TheSuperPixel/Embedded_Core_Boards/STM32H750/测试例程/DCMI-摄像头OV5640驱动/图像显示到800x480分辨率的屏幕/移植注意事项3.png

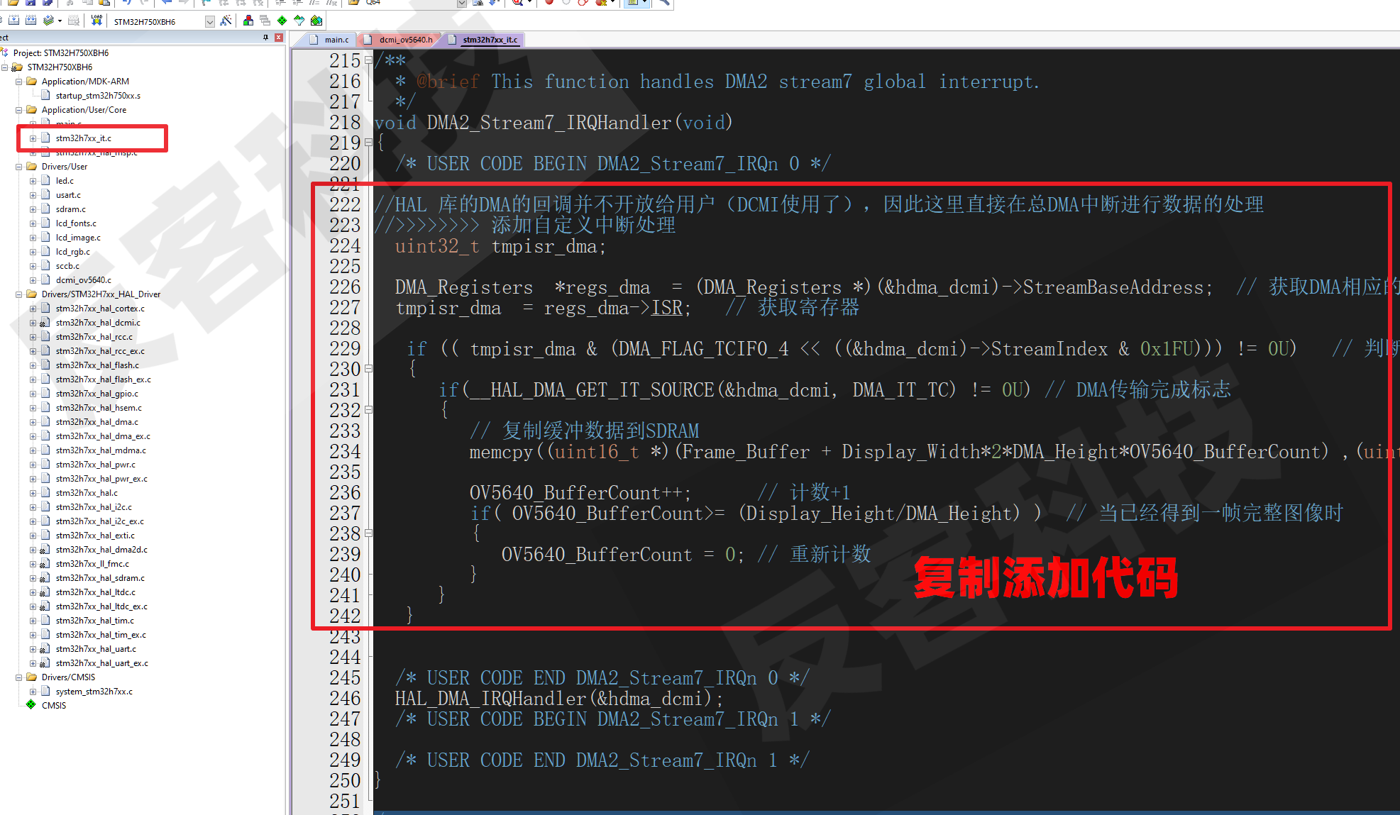
STM32H750/测试例程/DCMI-摄像头OV5640驱动/图像显示到800x480分辨率的屏幕/移植注意事项3.png
