TheSuperPixel/Embedded_Core_Boards/STM32H750/外壳/底板.SLDPRT

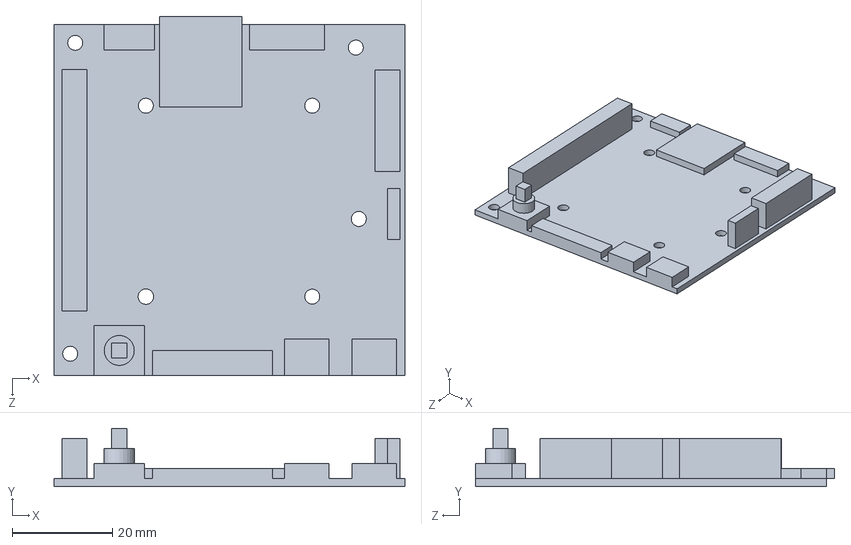
[picture p26: CAD file, 2026-02-05]
STM32H750/外壳/底板.SLDPRT
70.0 x 11.6 x 71.6 mm
