TheSuperPixel/Embedded_Core_Boards/XC7A35T/外壳/PCIE版本/输出图纸/中层亚克力.DXF

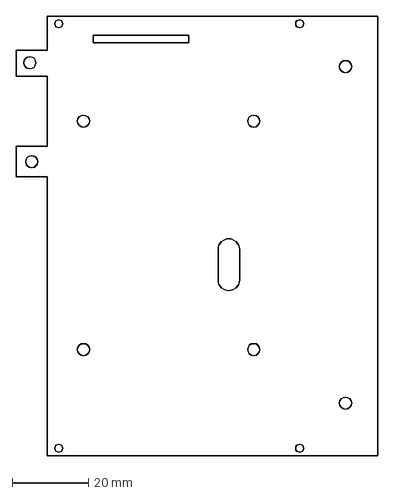
[picture p29: CAD file, 2026-03-31]
XC7A35T/外壳/PCIE版本/输出图纸/中层亚克力.DXF
94.6 x 115.0 mm
