TheSuperPixel/Embedded_Core_Boards/XC7A35T/外壳/全排针版本/底部亚克力.SLDPRT

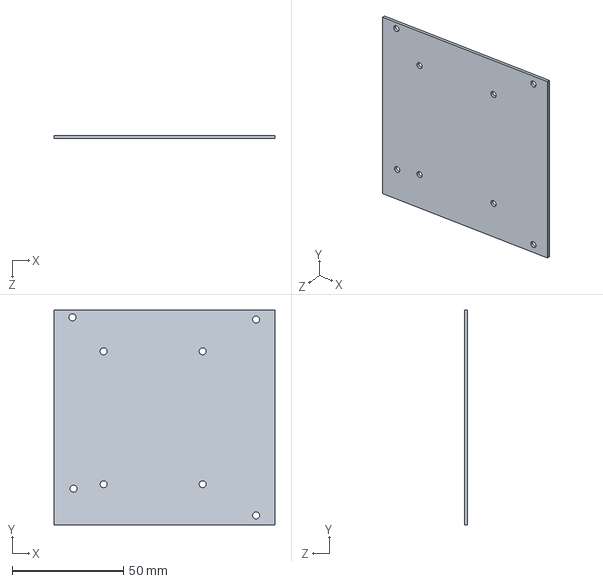
[picture p30: CAD file, 2026-02-06]
XC7A35T/外壳/全排针版本/底部亚克力.SLDPRT
99.3 x 96.6 x 1.50 mm
