TheSuperPixel/Embedded_Core_Boards/RK3588/外壳/输出图纸/MIPI屏幕亚克力.DXF

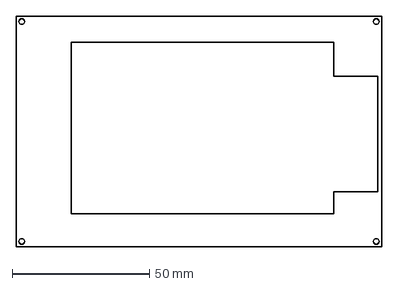
[picture p32: CAD file, 2026-03-31]
RK3588/外壳/输出图纸/MIPI屏幕亚克力.DXF
133.0 x 84.0 mm
