TheSuperPixel/Embedded_Core_Boards/STM32H750/外壳/输出图纸/顶层亚克力.DXF

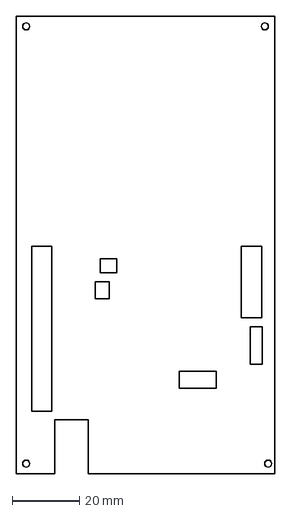
[picture p33: CAD file, 2026-03-31]
STM32H750/外壳/输出图纸/顶层亚克力.DXF
77.0 x 136.0 mm
