TheSuperPixel/Embedded_Core_Boards/XC7A35T/外壳/全排针版本/底部铜柱.SLDPRT

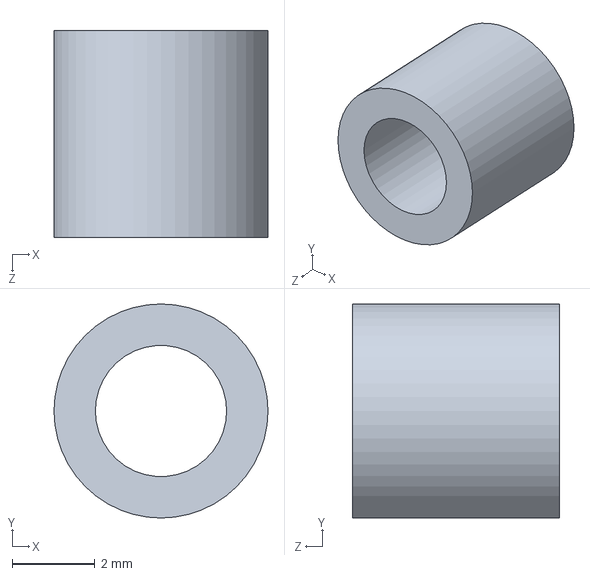
[picture p35: CAD file, 2026-02-06]
XC7A35T/外壳/全排针版本/底部铜柱.SLDPRT
5.17 x 5.17 x 5.00 mm
