TheSuperPixel/Embedded_Core_Boards/RK3588/外壳/输出图纸/底层亚克力.DXF

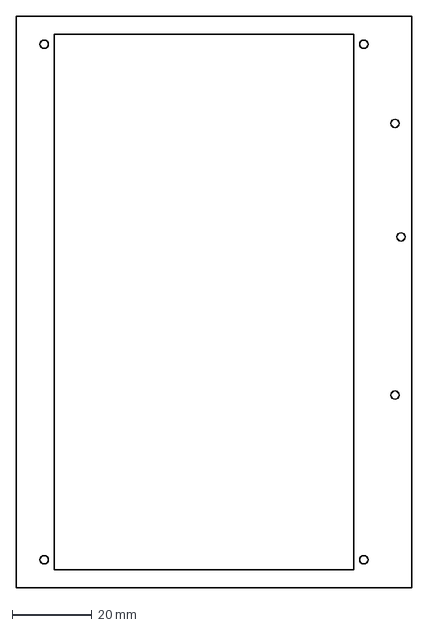
[picture p36: CAD file, 2026-03-31]
RK3588/外壳/输出图纸/底层亚克力.DXF
99.0 x 143.0 mm
