TheSuperPixel/Embedded_Core_Boards/XC7A35T/外壳/PCIE版本/输出图纸/顶层亚克力_无散热.DXF

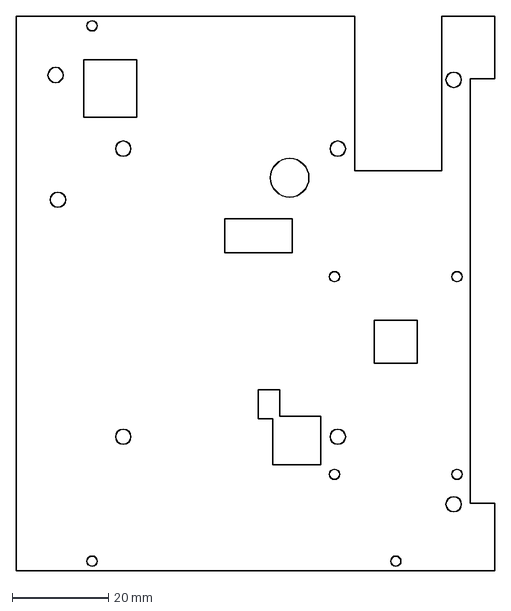
[picture p38: CAD file, 2026-03-31]
XC7A35T/外壳/PCIE版本/输出图纸/顶层亚克力_无散热.DXF
99.2 x 115.0 mm
