TheSuperPixel/Embedded_Core_Boards/XC7A35T/外壳/全排针版本/底板.SLDPRT

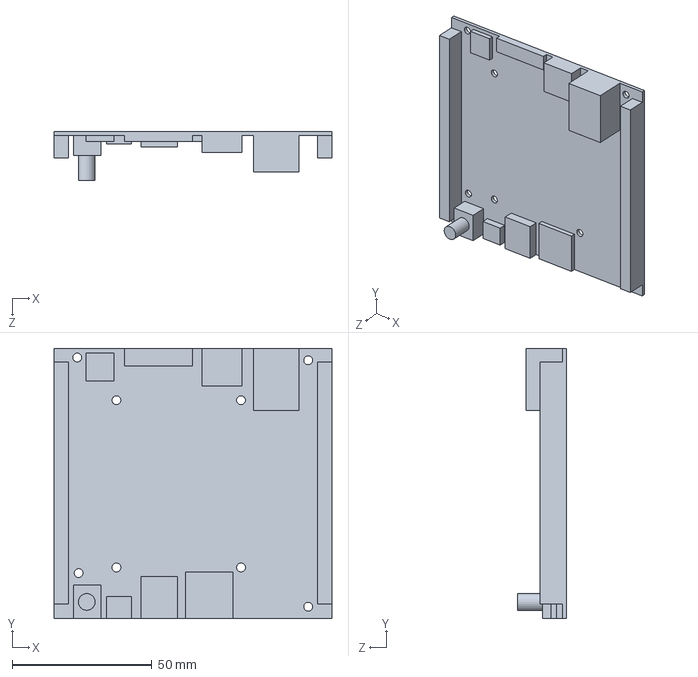
[picture p40: CAD file, 2026-02-06]
XC7A35T/外壳/全排针版本/底板.SLDPRT
99.3 x 96.6 x 17.5 mm
