TheSuperPixel/Embedded_Core_Boards/RK3588/外壳/MIPI屏幕.SLDPRT

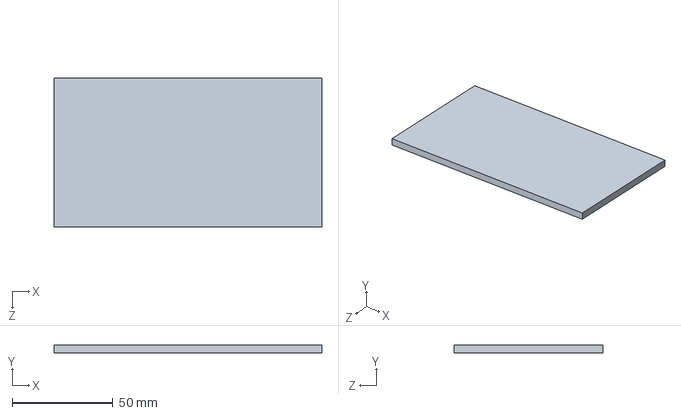
[picture p41: CAD file, 2026-02-09]
RK3588/外壳/MIPI屏幕.SLDPRT
133.0 x 4.00 x 74.0 mm
