TheSuperPixel/Embedded_Core_Boards/STM32H750/外壳/4.3寸RGB驱动.SLDPRT

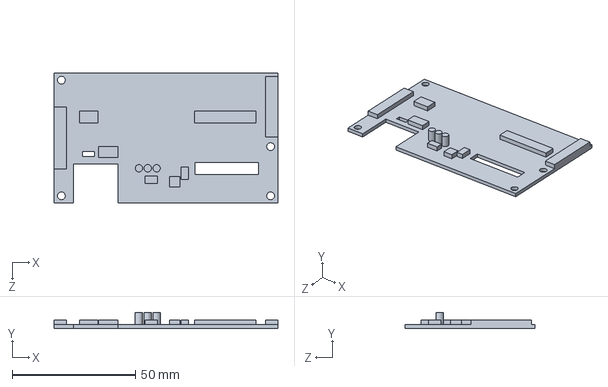
[picture p44: CAD file, 2026-02-05]
STM32H750/外壳/4.3寸RGB驱动.SLDPRT
91.0 x 6.60 x 53.0 mm
