TheSuperPixel/Embedded_Core_Boards/XC7A35T/外壳/PCIE版本/底层亚克力.SLDPRT

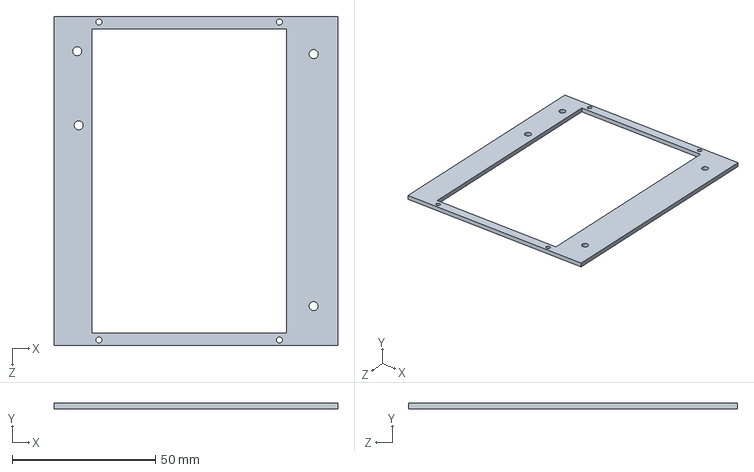
[picture p45: CAD file, 2026-02-06]
XC7A35T/外壳/PCIE版本/底层亚克力.SLDPRT
99.2 x 2.00 x 115.0 mm
