TheSuperPixel/Embedded_Core_Boards/STM32H750/外壳/OLED屏幕.SLDPRT

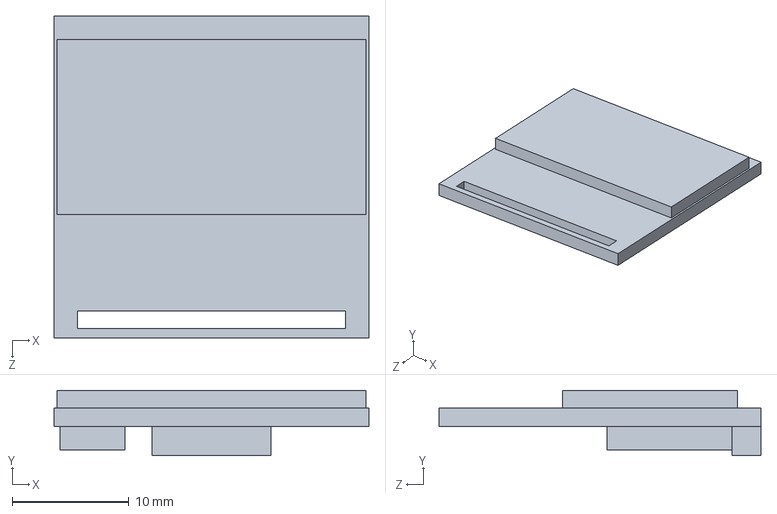
[picture p47: CAD file, 2026-02-05]
STM32H750/外壳/OLED屏幕.SLDPRT
27.0 x 5.60 x 27.6 mm
