TheSuperPixel/Embedded_Core_Boards/XC7A35T/外壳/全排针版本/顶部铜柱.SLDPRT

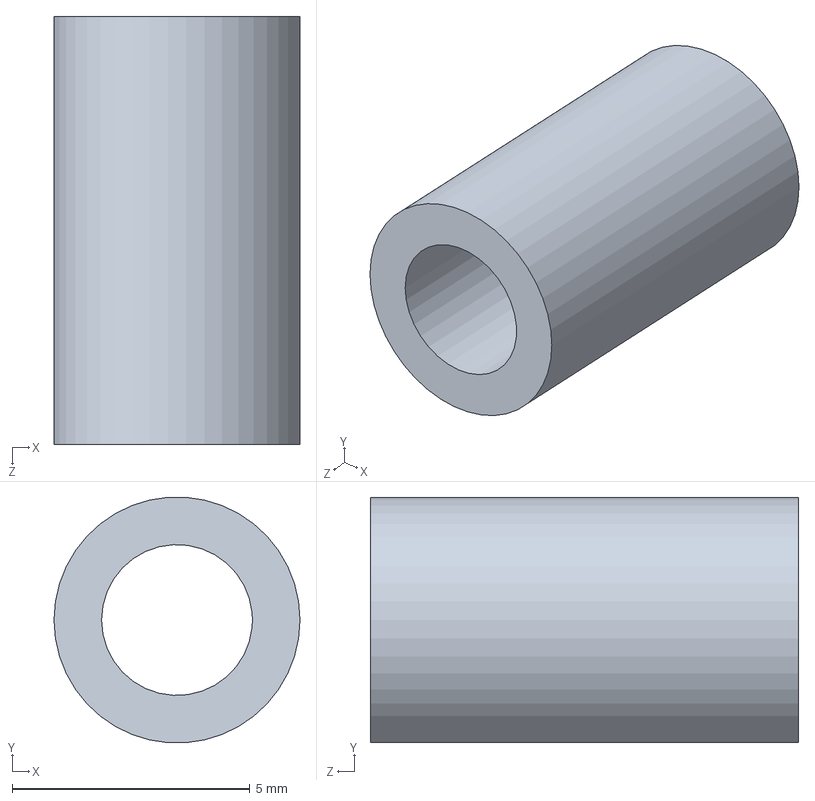
[picture p48: CAD file, 2026-02-06]
XC7A35T/外壳/全排针版本/顶部铜柱.SLDPRT
5.17 x 5.16 x 9.00 mm
