TheSuperPixel/Embedded_Core_Boards/RK3588/外壳/底板.SLDPRT

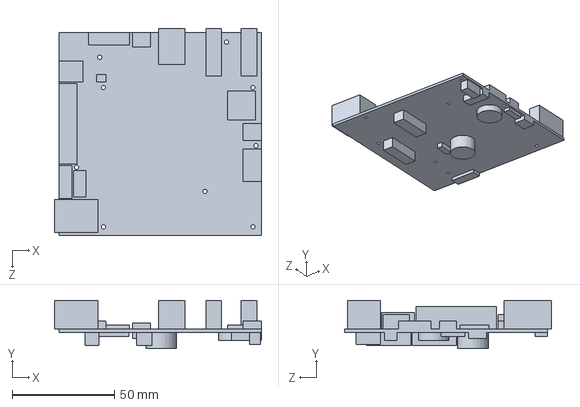
[picture p49: CAD file, 2026-02-09]
RK3588/外壳/底板.SLDPRT
101.1 x 23.6 x 101.0 mm
