TheSuperPixel/Embedded_Core_Boards/RK3588/外壳/风扇.SLDPRT

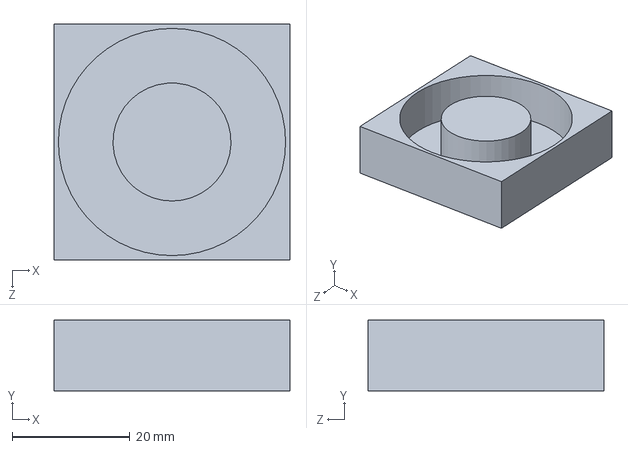
[picture p50: CAD file, 2026-02-09]
RK3588/外壳/风扇.SLDPRT
40.0 x 12.0 x 40.0 mm
