TheSuperPixel/Embedded_Core_Boards/STM32H750/外壳/核心板.SLDPRT

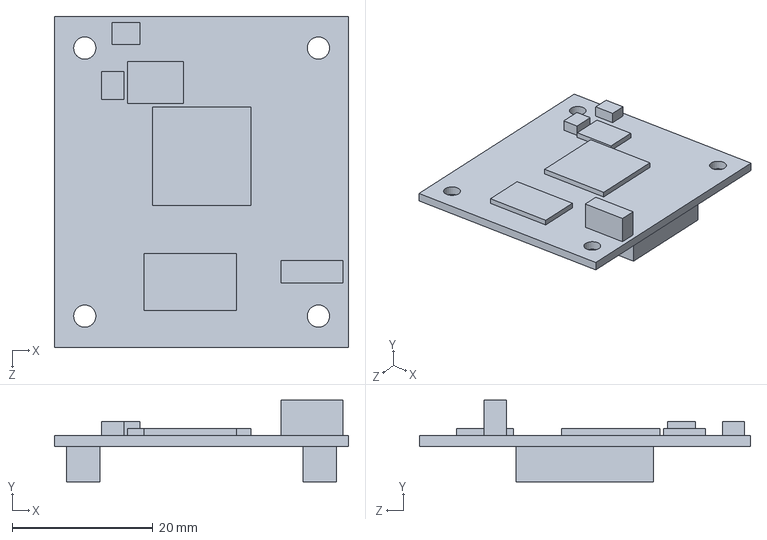
[picture p52: CAD file, 2026-02-05]
STM32H750/外壳/核心板.SLDPRT
41.9 x 11.6 x 47.1 mm
