TheSuperPixel/Embedded_Core_Boards/RK3588/外壳/镜头模组.SLDPRT

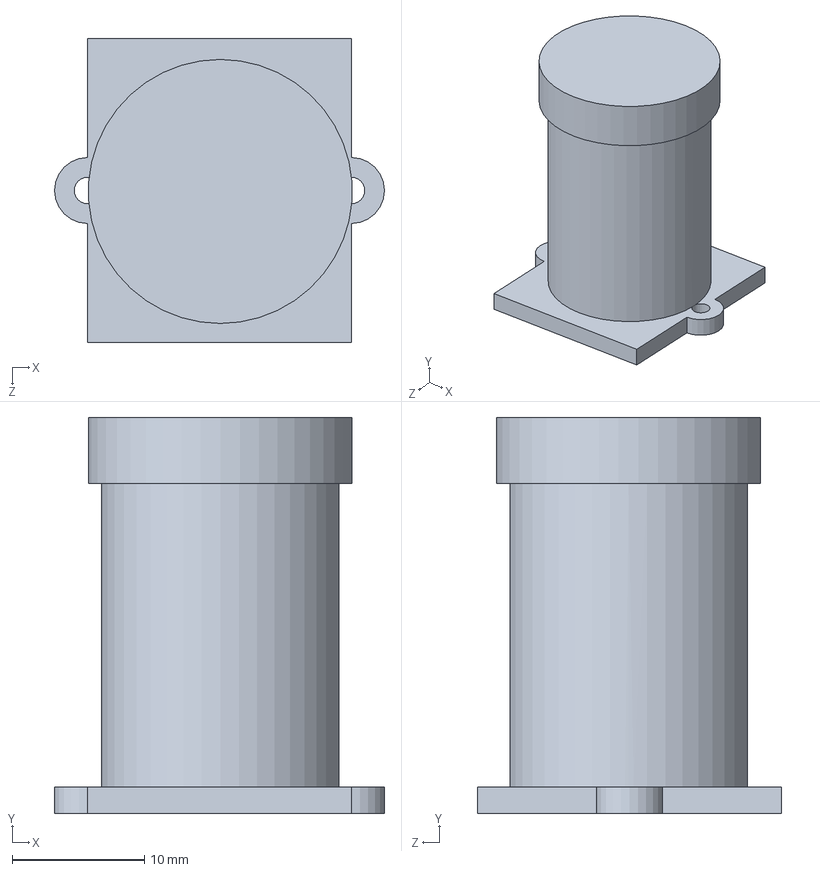
[picture p53: CAD file, 2026-02-09]
RK3588/外壳/镜头模组.SLDPRT
25.0 x 30.0 x 23.0 mm
