TheSuperPixel/Embedded_Core_Boards/STM32H750/外壳/MCU LCD屏幕.SLDPRT

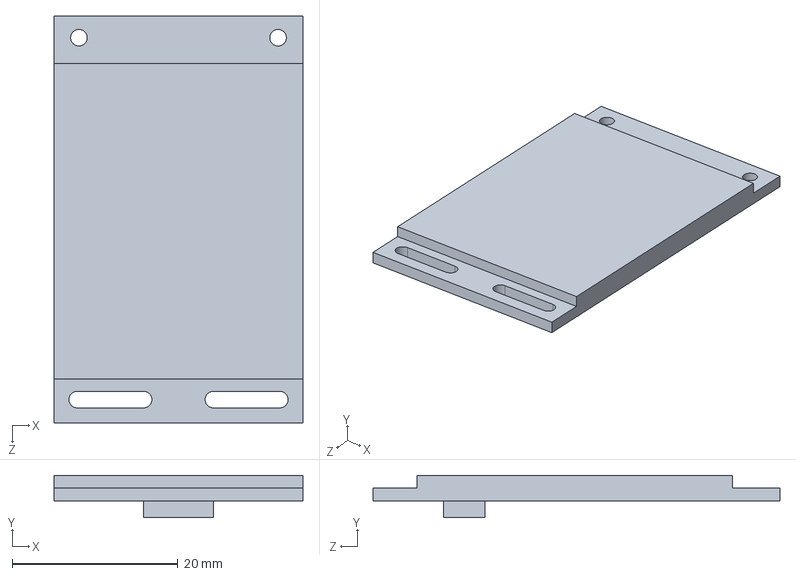
[picture p54: CAD file, 2026-02-05]
STM32H750/外壳/MCU LCD屏幕.SLDPRT
30.0 x 5.10 x 49.0 mm
