TheSuperPixel/Embedded_Core_Boards/XC7A35T/外壳/PCIE版本/底板_PCIE.SLDPRT

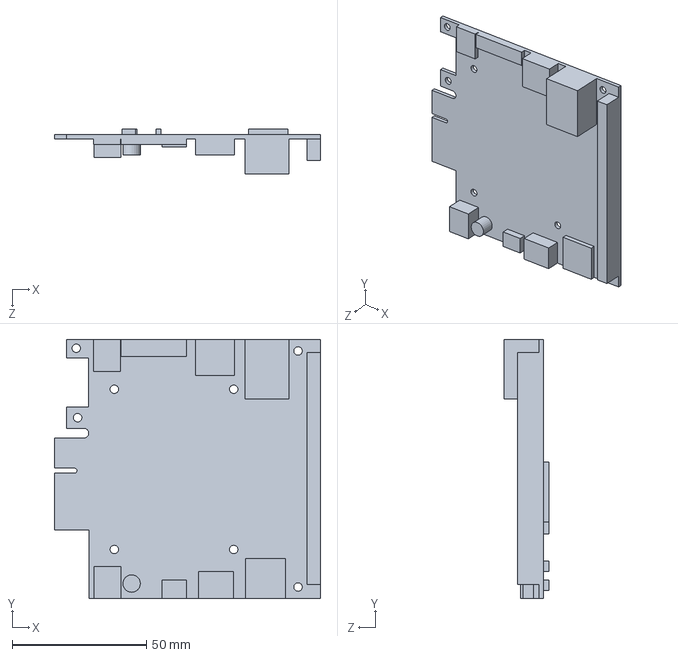
[picture p55: CAD file, 2026-02-06]
XC7A35T/外壳/PCIE版本/底板_PCIE.SLDPRT
99.2 x 96.6 x 16.6 mm
