TheSuperPixel/Embedded_Core_Boards/RK3588/外壳/顶层亚克力.SLDPRT

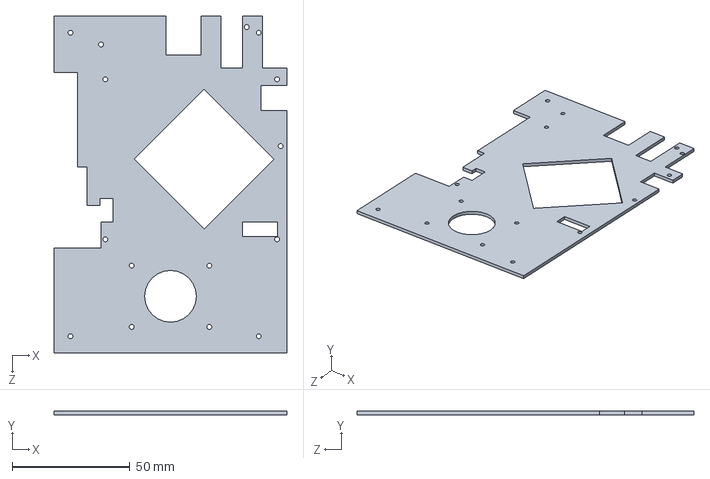
[picture p56: CAD file, 2026-02-09]
RK3588/外壳/顶层亚克力.SLDPRT
99.0 x 1.60 x 143.0 mm
