TheSuperPixel/Embedded_Core_Boards/STM32H750/外壳/OV5640摄像头.SLDPRT

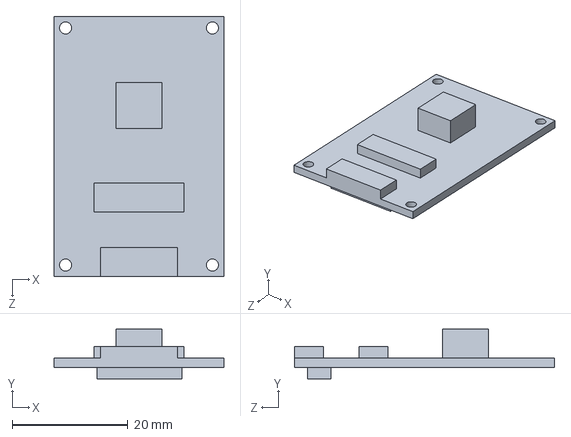
[picture p57: CAD file, 2026-02-05]
STM32H750/外壳/OV5640摄像头.SLDPRT
29.4 x 8.60 x 45.0 mm
