TheSuperPixel/Embedded_Core_Boards/RK3588/外壳/核心板.SLDPRT

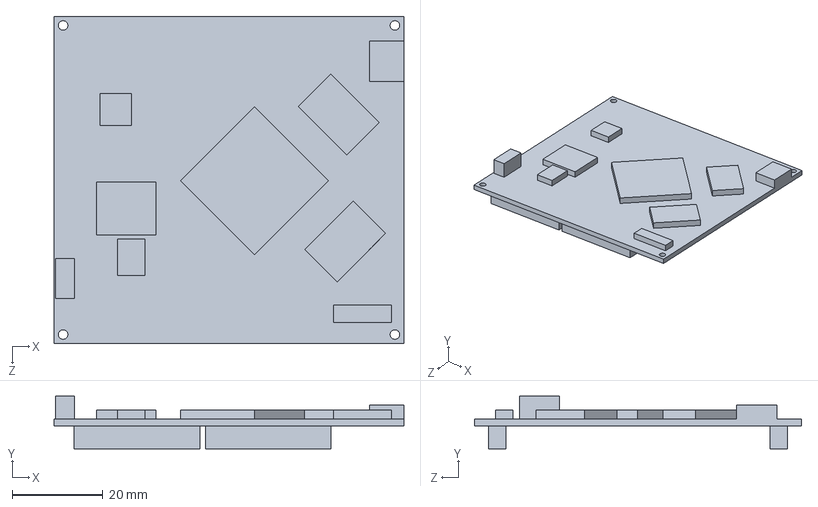
[picture p58: CAD file, 2026-02-09]
RK3588/外壳/核心板.SLDPRT
77.0 x 11.6 x 72.0 mm
