TheSuperPixel/Embedded_Core_Boards/STM32H750/外壳/中层亚克力.SLDPRT

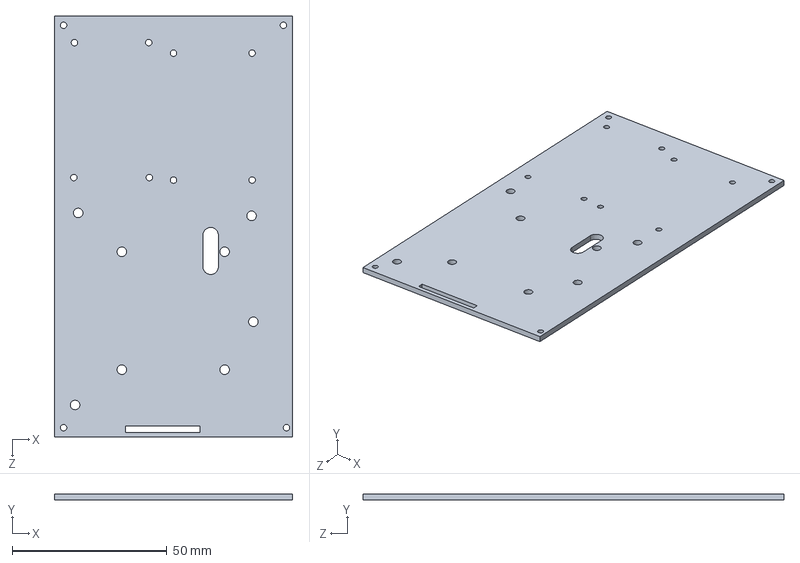
[picture p59: CAD file, 2026-02-05]
STM32H750/外壳/中层亚克力.SLDPRT
77.0 x 2.00 x 136.0 mm
