TheSuperPixel/Embedded_Core_Boards/XC7A35T/外壳/PCIE版本/核心板.SLDPRT

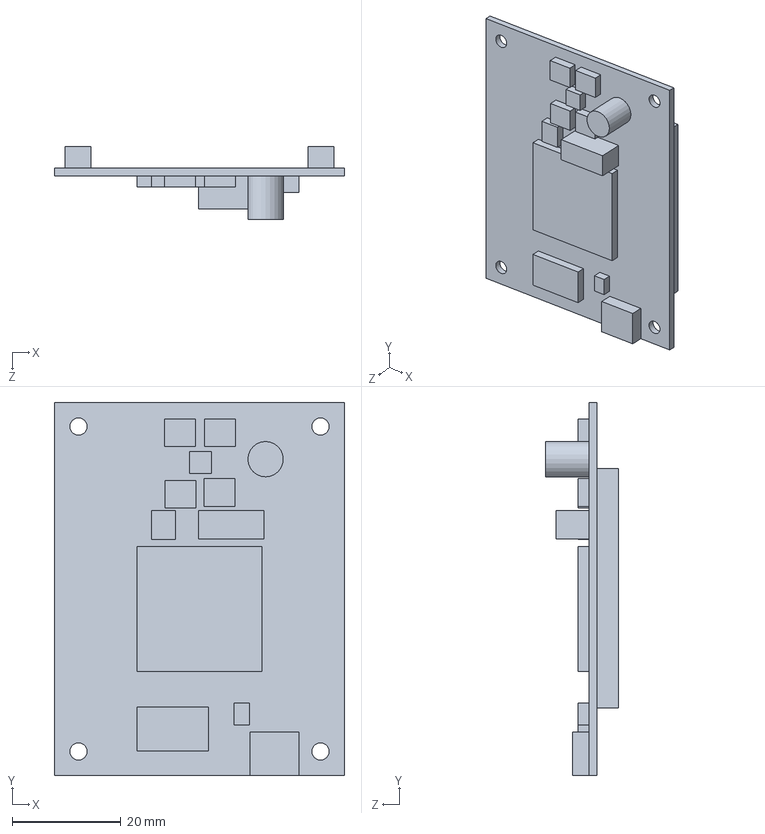
[picture p60: CAD file, 2026-02-06]
XC7A35T/外壳/PCIE版本/核心板.SLDPRT
53.3 x 68.6 x 13.5 mm
