TheSuperPixel/Embedded_Core_Boards/XC7A35T/外壳/PCIE版本/4.3寸RGB屏幕.SLDPRT

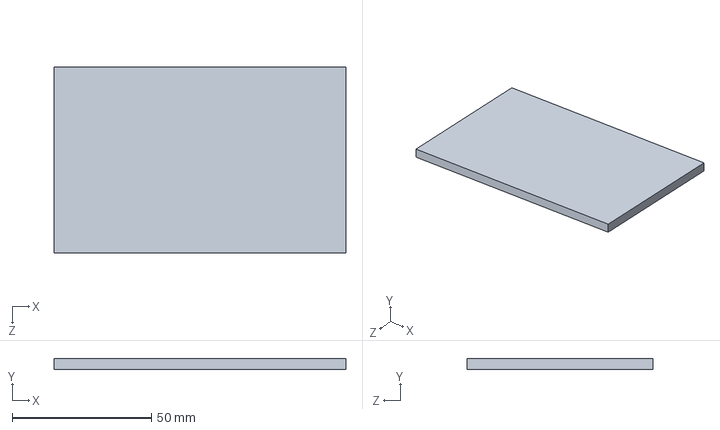
[picture p61: CAD file, 2026-02-05]
XC7A35T/外壳/PCIE版本/4.3寸RGB屏幕.SLDPRT
105.0 x 4.00 x 67.0 mm
