TheSuperPixel/Embedded_Core_Boards/XC7A35T/外壳/PCIE版本/屏幕亚克力.SLDPRT

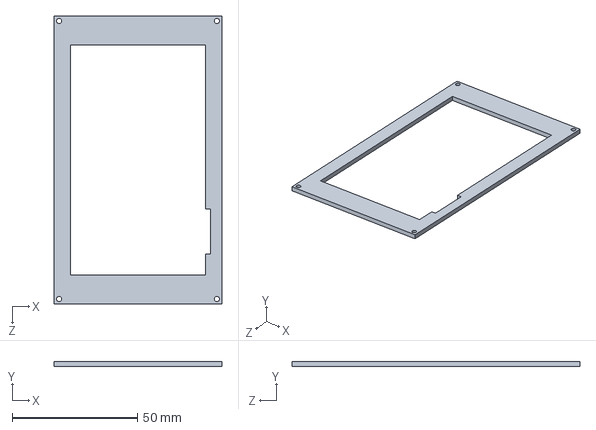
[picture p62: CAD file, 2026-02-05]
XC7A35T/外壳/PCIE版本/屏幕亚克力.SLDPRT
67.0 x 2.00 x 115.0 mm
