TheSuperPixel/Embedded_Core_Boards/RK3588/外壳/MIPI屏幕亚克力.SLDPRT

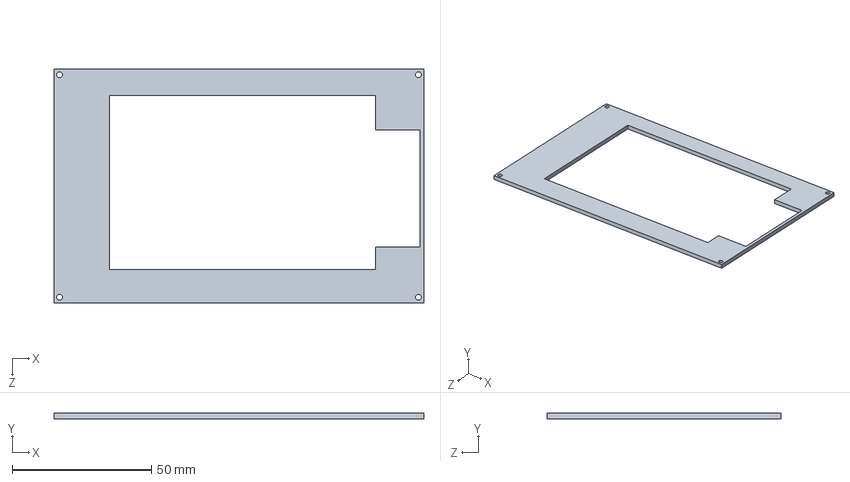
[picture p63: CAD file, 2026-02-09]
RK3588/外壳/MIPI屏幕亚克力.SLDPRT
133.0 x 2.00 x 84.0 mm
