TheSuperPixel/Embedded_Core_Boards/XC7A35T/XC7A35T核心板/Project Outputs for xc7a35t/Sheet1.pdf

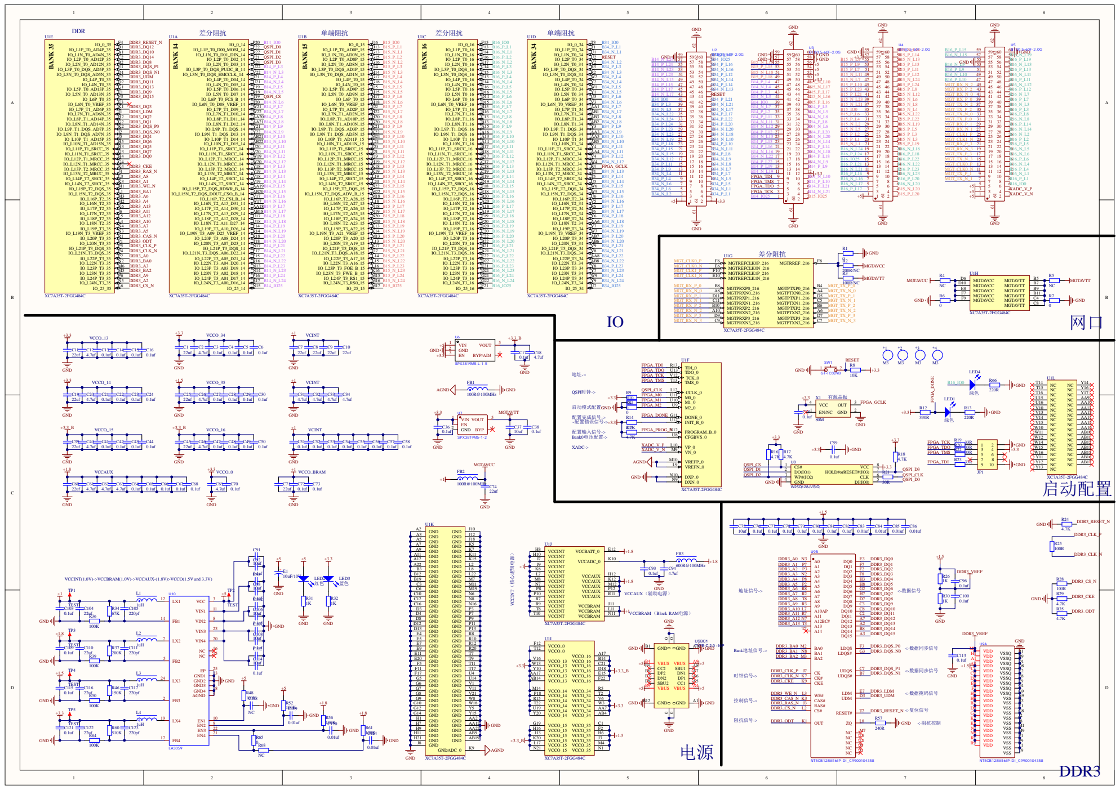
[picture p111: page 1]

VCCINT(1.0V)->VCCBRAM(1.0V)->VCCAUX-(1.8V)>VCCO(1.5V and 3.3V)
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
