TheSuperPixel/Embedded_Core_Boards/STM32H750/底板v2/Project Outputs for STM32H750底板/Sheet1.pdf

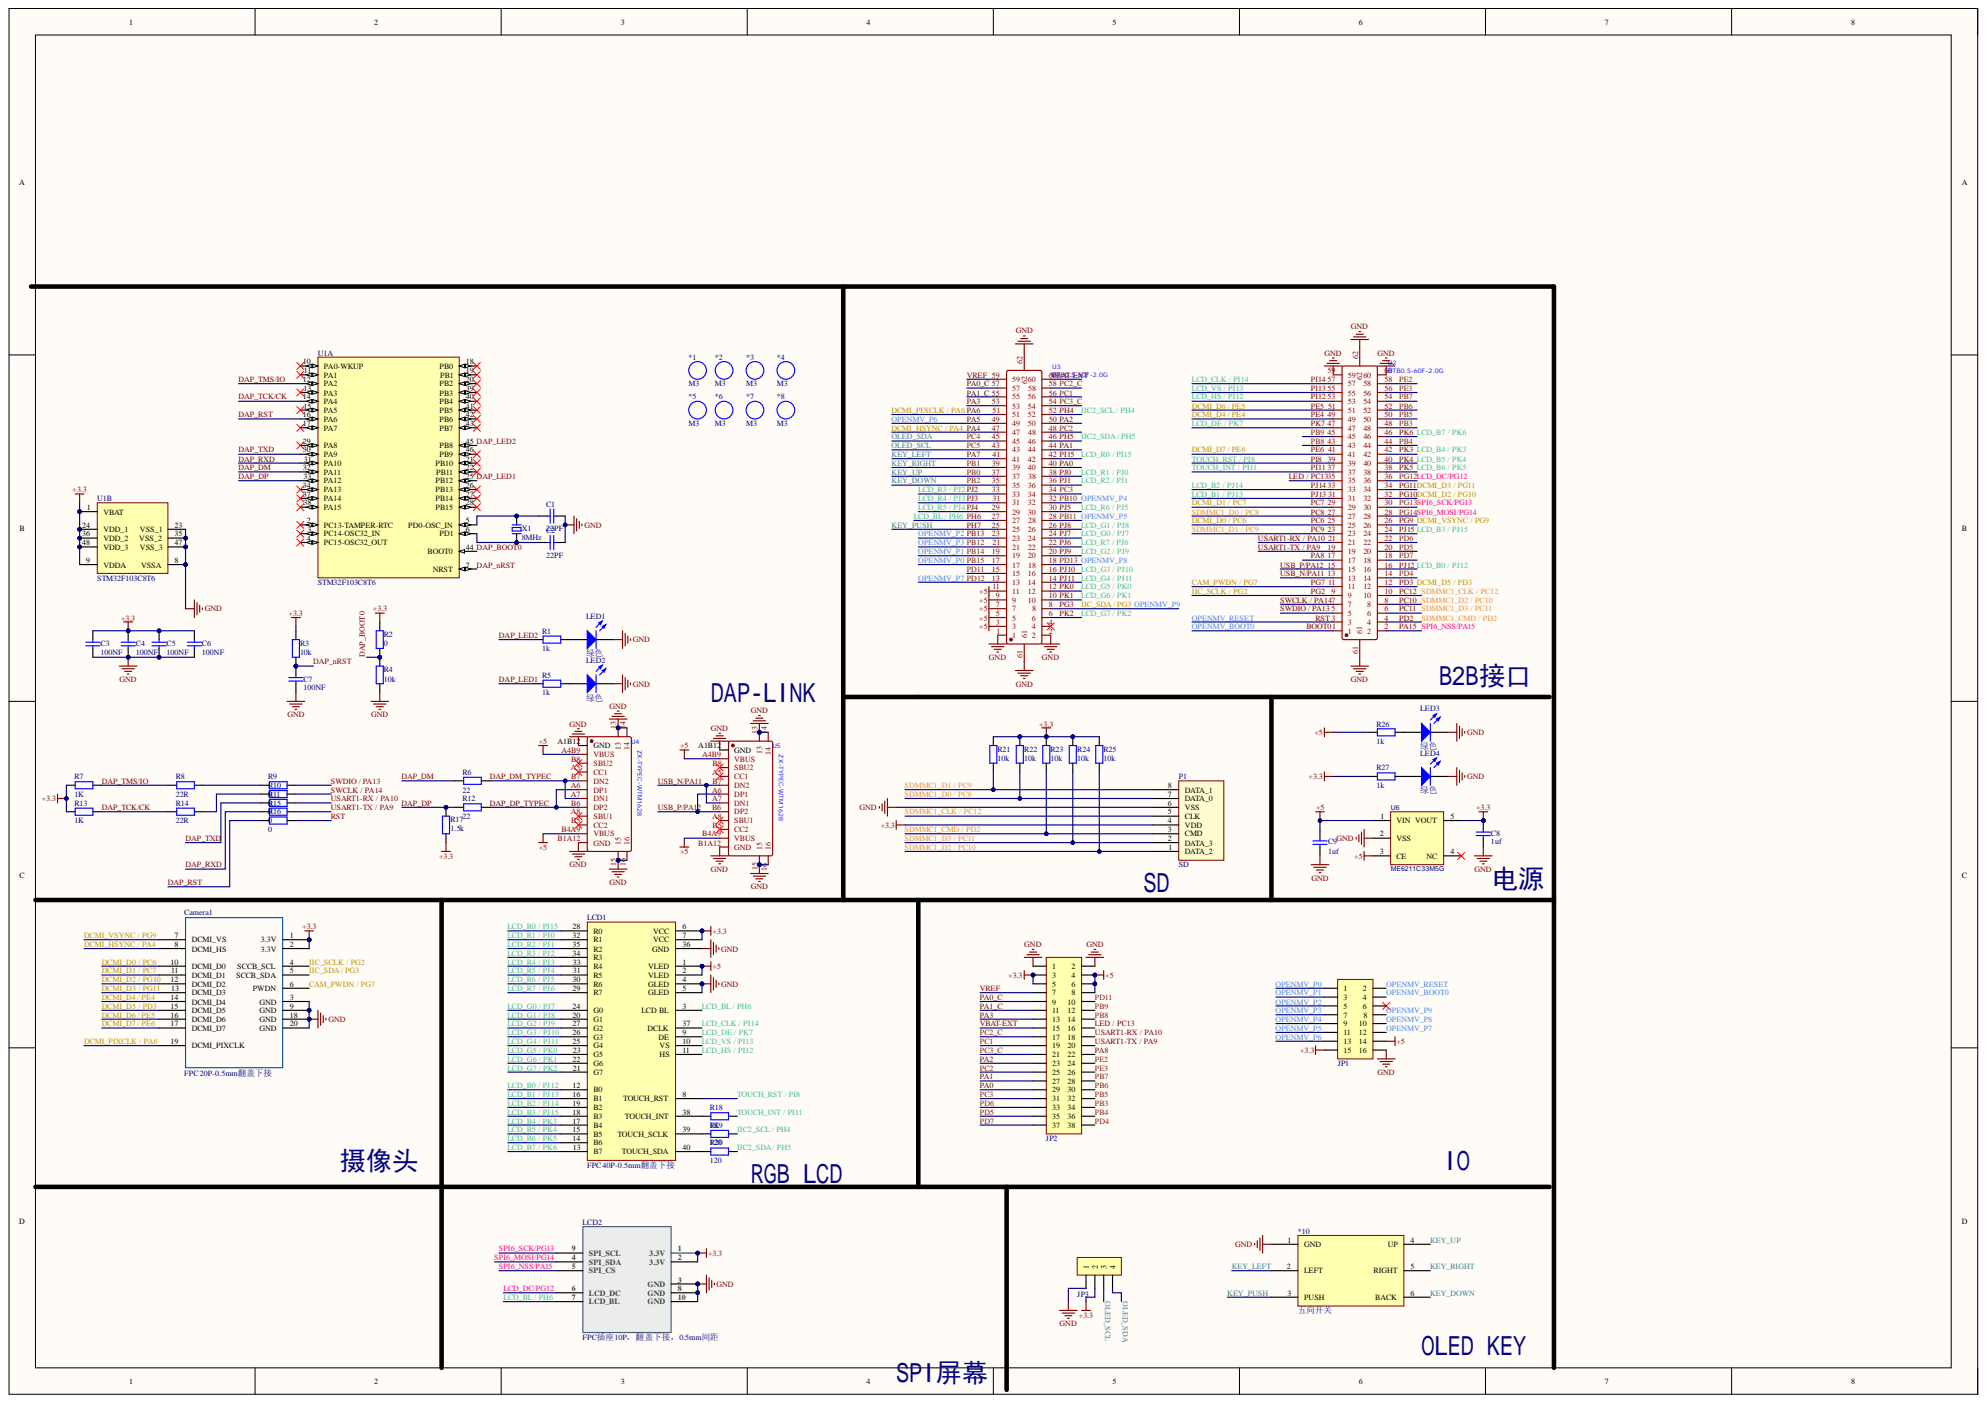
[picture p124: page 1]
