TheSuperPixel/Embedded_Core_Boards/XC7A35T/XC7A35T底板v1/Project Outputs for XC7A35T底板/Sheet1.pdf

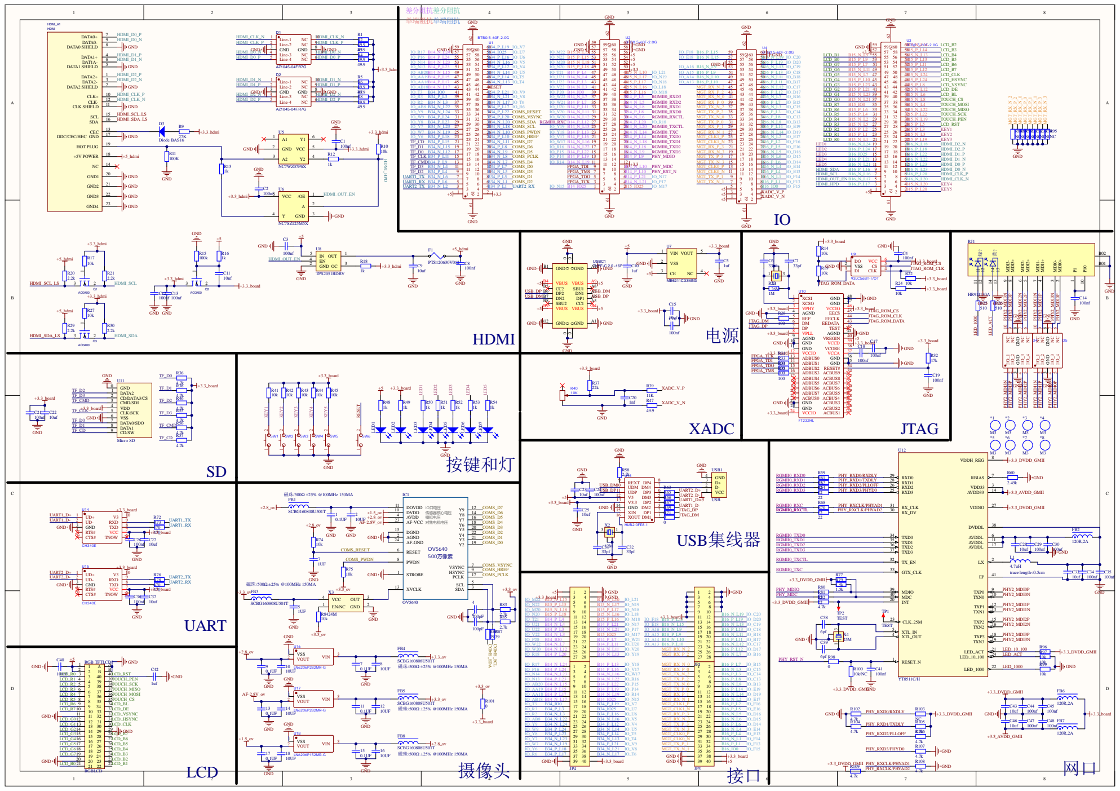
[picture p125: page 1]

I/O_4 5 NC 6 NC 7 GND 8 NC 9 NC 10
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
