TheSuperPixel/Embedded_Core_Boards/STM32H750/STM32H750核心板v1/Project Outputs for STM32H750核心板/Sheet1.pdf

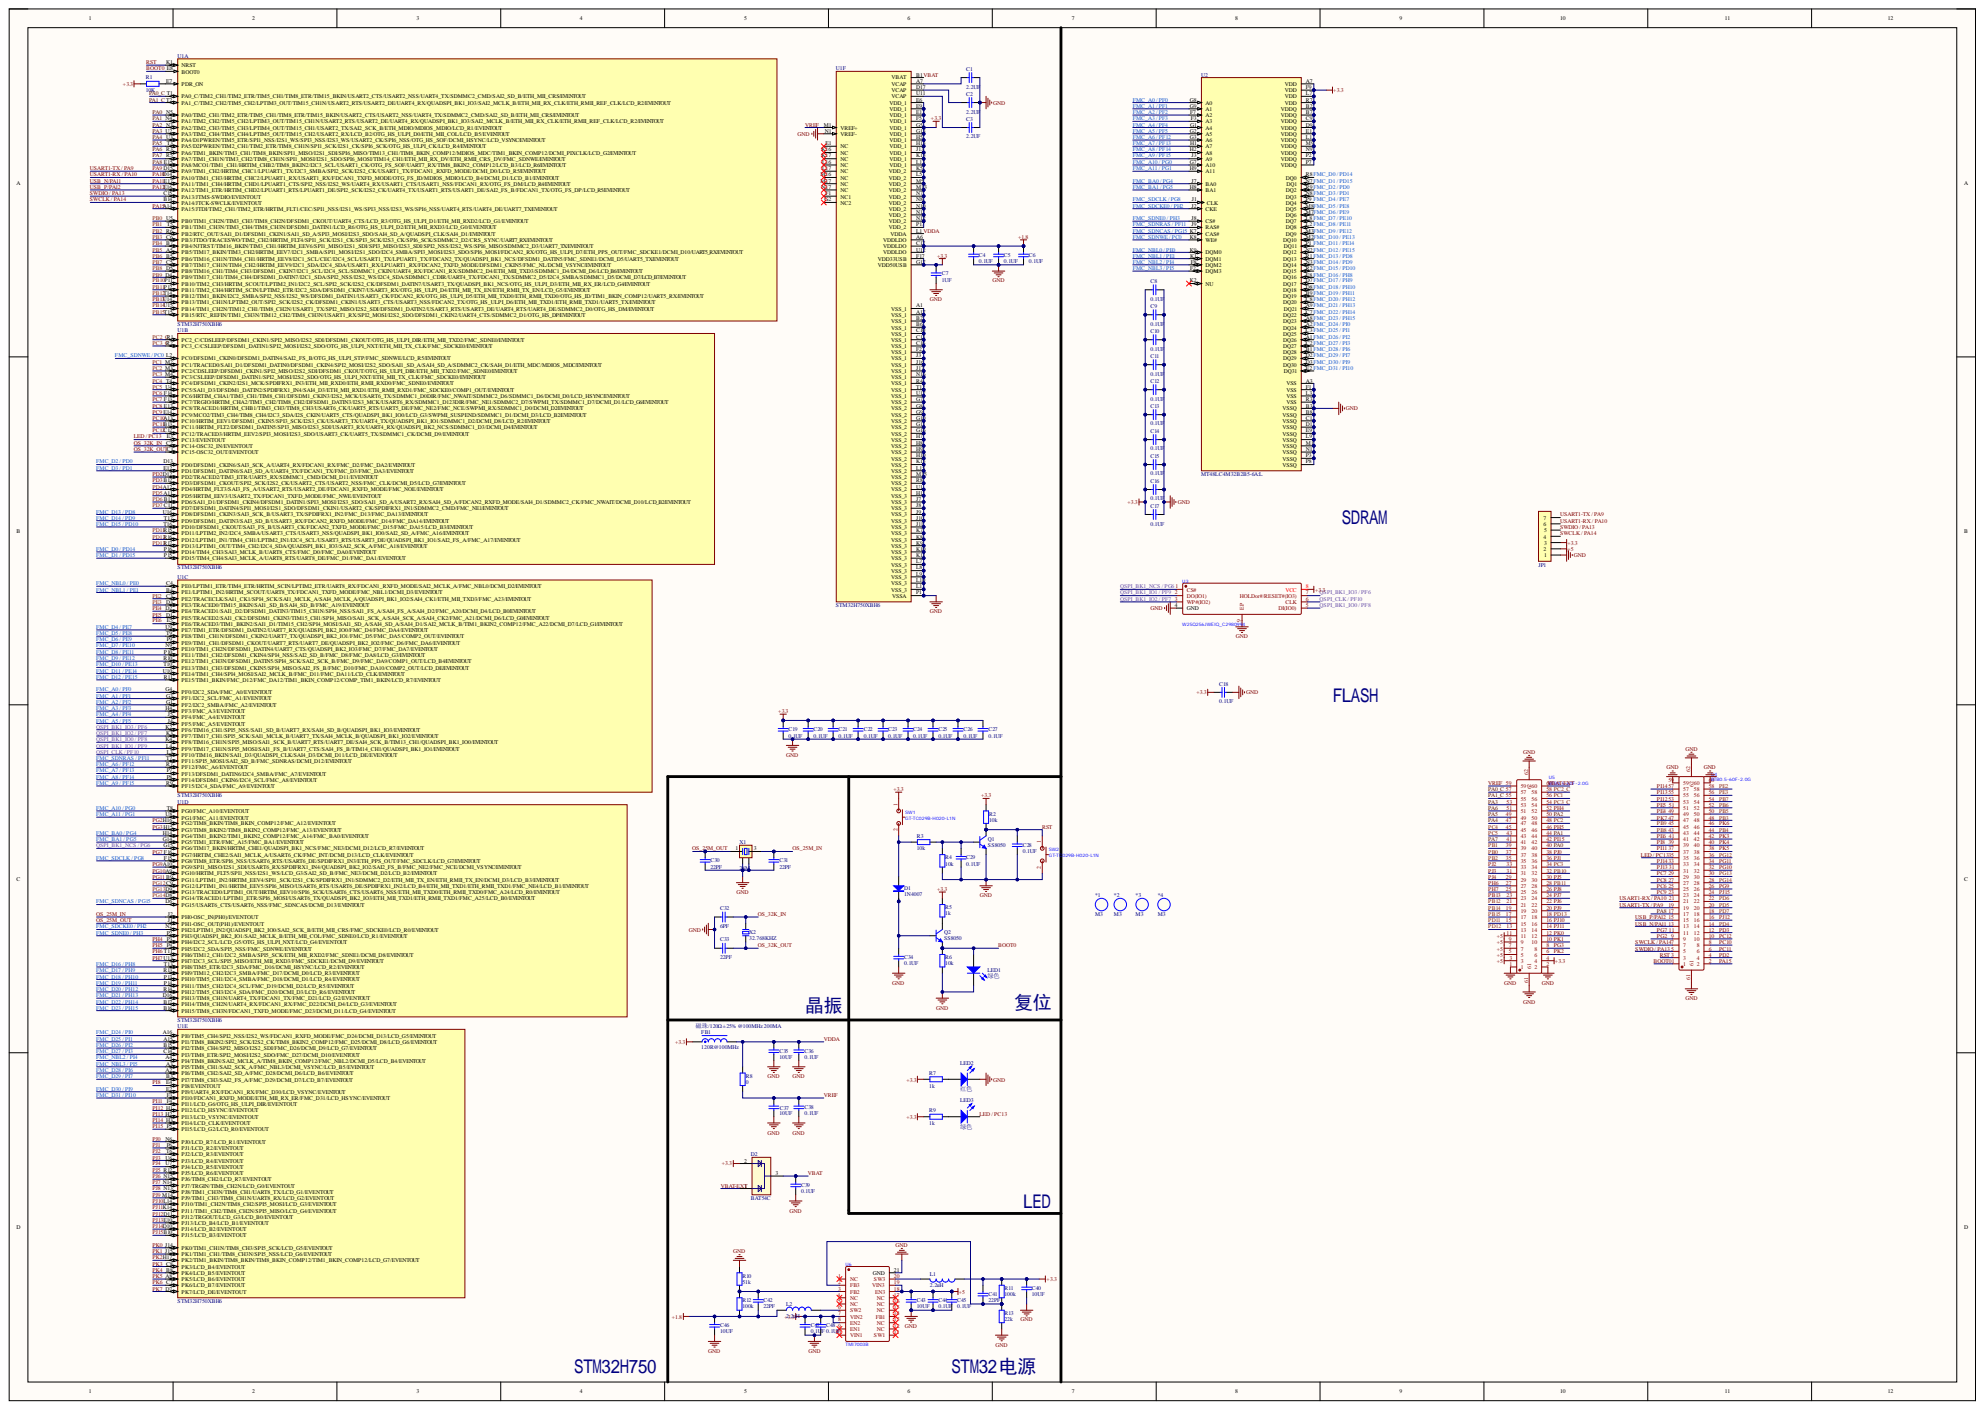
[picture p127: page 1]
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
