TheSuperPixel/Embedded_Core_Boards/STM32H750/底板v1/Project Outputs for STM32H750底板/Sheet1.pdf

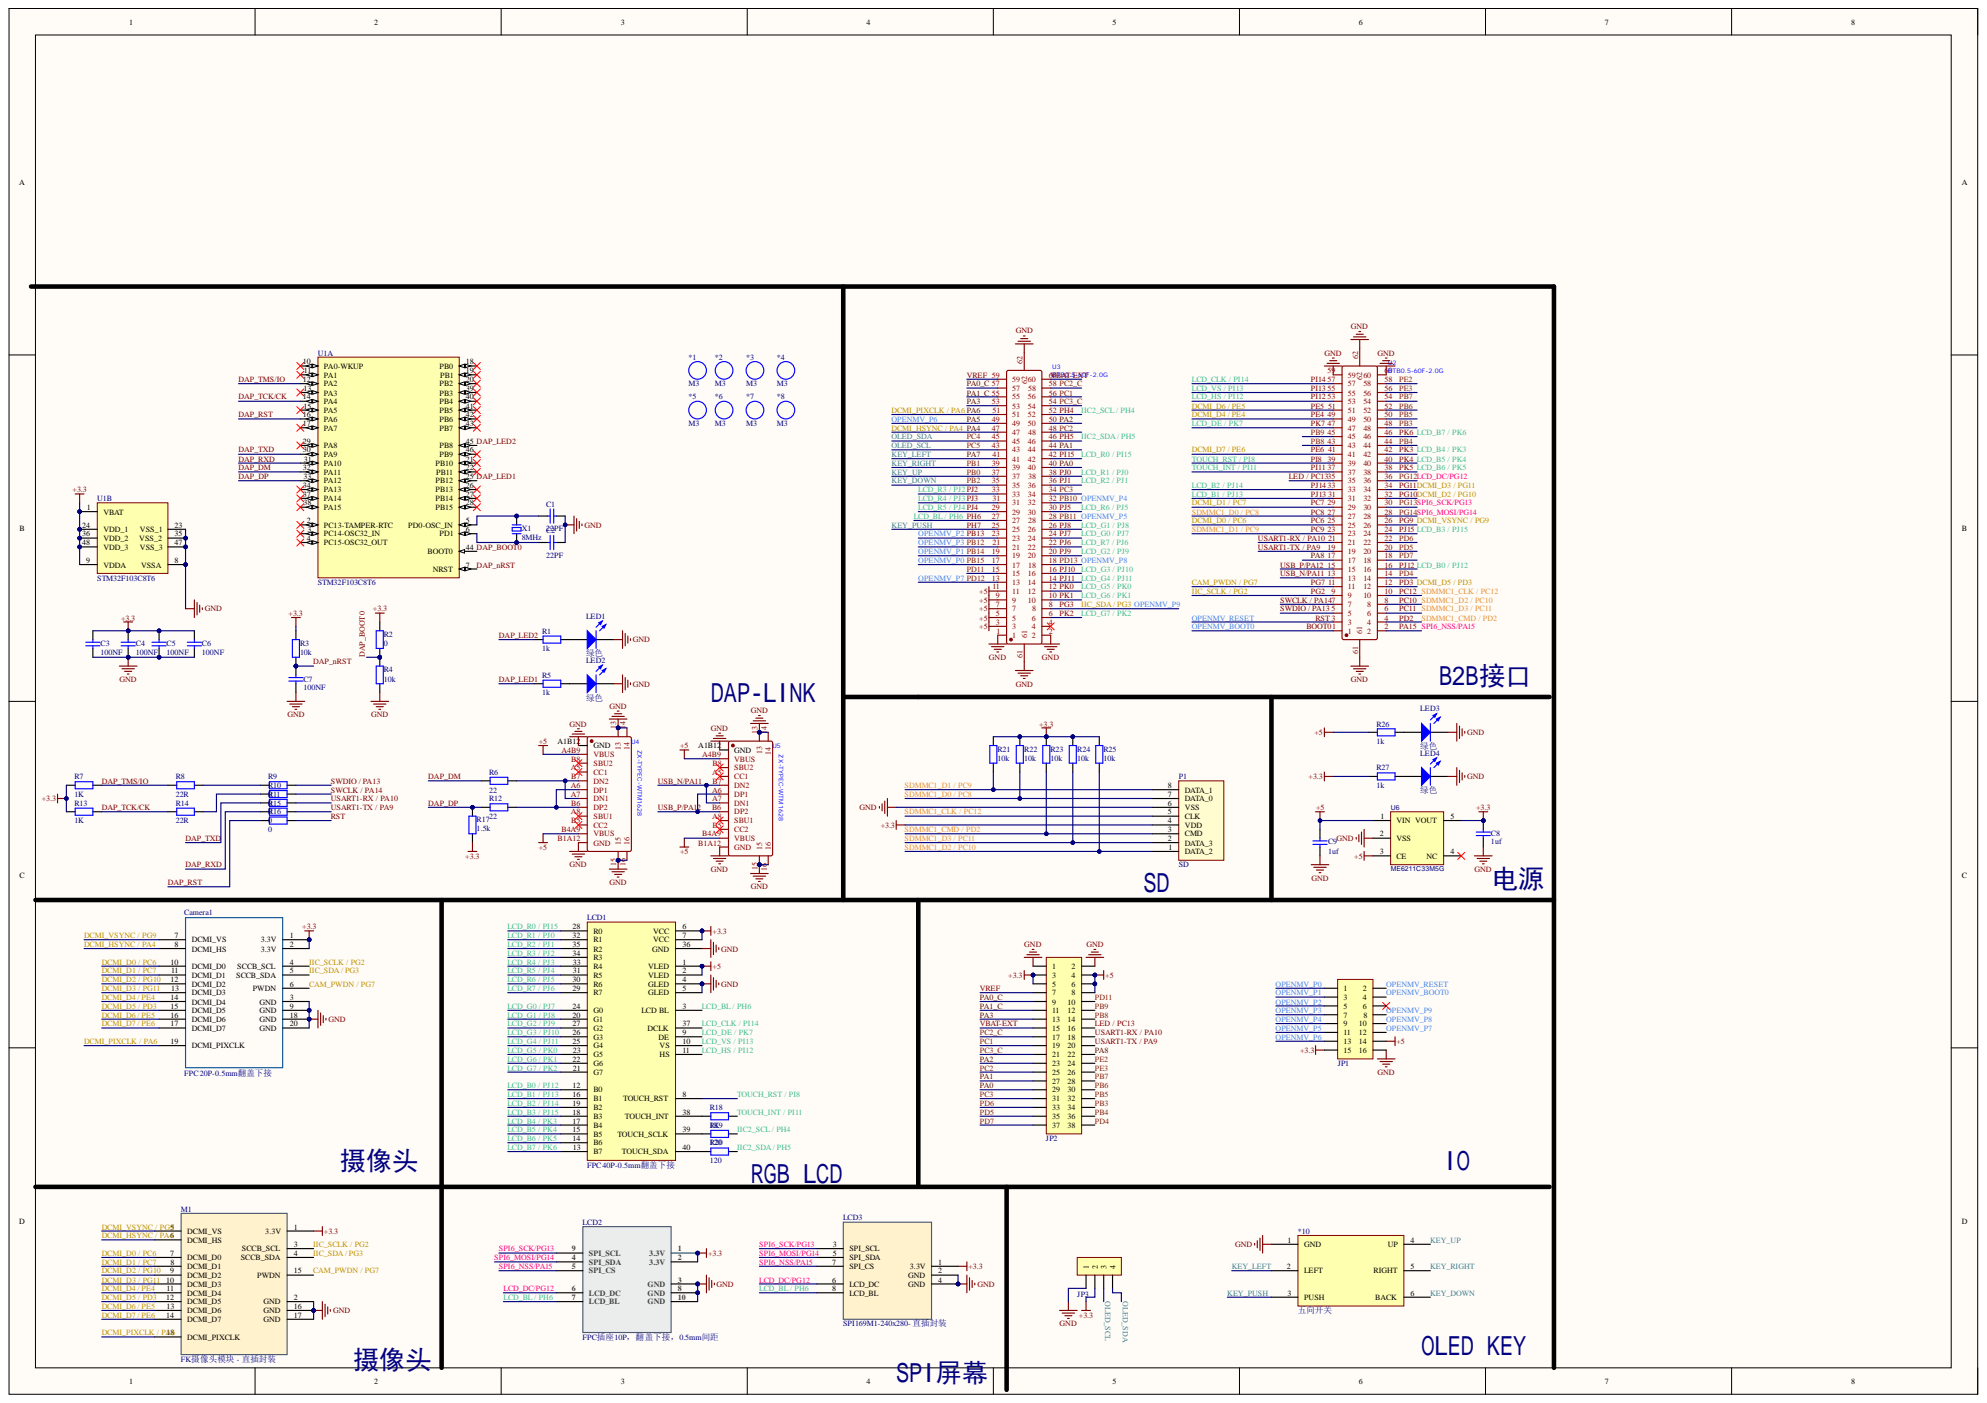
[picture p128: page 1]
