TheSuperPixel/Embedded_Core_Boards/XC7A35T/测试例程/39b_ov5640_lcd/prj/ov5640_lcd.srcs/constrs_1/new/pin.xdc

create_clock -period 20.000 -name sys_clk [get_ports sys_clk]
set_property CLOCK_DEDICATED_ROUTE FALSE [get_nets sys_clk]
set_property PACKAGE_PIN R4 [get_ports sys_clk]
set_property IOSTANDARD LVCMOS33 [get_ports sys_clk]
set_property IOSTANDARD LVCMOS33 [get_ports sys_rst_n]
set_property PACKAGE_PIN U2 [get_ports sys_rst_n]

#底板RGB LCD 需要调换R与B才能正常显示
set_property -dict {PACKAGE_PIN K21 IOSTANDARD LVCMOS33} [get_ports {lcd_rgb[0]}]
set_property -dict {PACKAGE_PIN K22 IOSTANDARD LVCMOS33} [get_ports {lcd_rgb[1]}]
set_property -dict {PACKAGE_PIN L20 IOSTANDARD LVCMOS33} [get_ports {lcd_rgb[2]}]
set_property -dict {PACKAGE_PIN L19 IOSTANDARD LVCMOS33} [get_ports {lcd_rgb[3]}]
set_property -dict {PACKAGE_PIN K19 IOSTANDARD LVCMOS33} [get_ports {lcd_rgb[4]}]
set_property -dict {PACKAGE_PIN K18 IOSTANDARD LVCMOS33} [get_ports {lcd_rgb[5]}]
set_property -dict {PACKAGE_PIN J20 IOSTANDARD LVCMOS33} [get_ports {lcd_rgb[6]}]
set_property -dict {PACKAGE_PIN J19 IOSTANDARD LVCMOS33} [get_ports {lcd_rgb[7]}]

set_property -dict {PACKAGE_PIN J17 IOSTANDARD LVCMOS33} [get_ports {lcd_rgb[8]}]
set_property -dict {PACKAGE_PIN K16 IOSTANDARD LVCMOS33} [get_ports {lcd_rgb[9]}]
set_property -dict {PACKAGE_PIN K17 IOSTANDARD LVCMOS33} [get_ports {lcd_rgb[10]}]
set_property -dict {PACKAGE_PIN L16 IOSTANDARD LVCMOS33} [get_ports {lcd_rgb[11]}]
set_property -dict {PACKAGE_PIN M21 IOSTANDARD LVCMOS33} [get_ports {lcd_rgb[12]}]
set_property -dict {PACKAGE_PIN H22 IOSTANDARD LVCMOS33} [get_ports {lcd_rgb[13]}]
set_property -dict {PACKAGE_PIN J21 IOSTANDARD LVCMOS33} [get_ports {lcd_rgb[14]}]
set_property -dict {PACKAGE_PIN J22 IOSTANDARD LVCMOS33} [get_ports {lcd_rgb[15]}]

set_property -dict {PACKAGE_PIN G13 IOSTANDARD LVCMOS33} [get_ports {lcd_rgb[16]}]
set_property -dict {PACKAGE_PIN H13 IOSTANDARD LVCMOS33} [get_ports {lcd_rgb[17]}]
set_property -dict {PACKAGE_PIN G15 IOSTANDARD LVCMOS33} [get_ports {lcd_rgb[18]}]
set_property -dict {PACKAGE_PIN H15 IOSTANDARD LVCMOS33} [get_ports {lcd_rgb[19]}]
set_property -dict {PACKAGE_PIN G16 IOSTANDARD LVCMOS33} [get_ports {lcd_rgb[20]}]
set_property -dict {PACKAGE_PIN G17 IOSTANDARD LVCMOS33} [get_ports {lcd_rgb[21]}]
set_property -dict {PACKAGE_PIN H17 IOSTANDARD LVCMOS33} [get_ports {lcd_rgb[22]}]
set_property -dict {PACKAGE_PIN J16 IOSTANDARD LVCMOS33} [get_ports {lcd_rgb[23]}]

set_property -dict {PACKAGE_PIN M15 IOSTANDARD LVCMOS33} [get_ports lcd_hs]
set_property -dict {PACKAGE_PIN H20 IOSTANDARD LVCMOS33} [get_ports lcd_vs]
set_property -dict {PACKAGE_PIN H19 IOSTANDARD LVCMOS33} [get_ports lcd_de]
set_property -dict {PACKAGE_PIN H18 IOSTANDARD LVCMOS33} [get_ports lcd_bl]
set_property -dict {PACKAGE_PIN M16 IOSTANDARD LVCMOS33} [get_ports lcd_pclk]
set_property -dict {PACKAGE_PIN J15 IOSTANDARD LVCMOS33} [get_ports lcd_rst]

#CAMERA

#摄像头接口的时钟
create_clock -period 40.000 -name cmos_pclk [get_ports cam_pclk]
set_property CLOCK_DEDICATED_ROUTE FALSE [get_nets cam_pclk_IBUF]
set_property -dict {PACKAGE_PIN AB2 IOSTANDARD LVCMOS33} [get_ports cam_pclk]
set_property -dict {PACKAGE_PIN AA8 IOSTANDARD LVCMOS33} [get_ports cam_rst_n]
set_property -dict {PACKAGE_PIN AB5 IOSTANDARD LVCMOS33} [get_ports cam_pwdn]
set_property -dict {PACKAGE_PIN AA1 IOSTANDARD LVCMOS33 IOB TRUE} [get_ports {cam_data[0]}]
set_property -dict {PACKAGE_PIN W1 IOSTANDARD LVCMOS33 IOB TRUE} [get_ports {cam_data[1]}]
set_property -dict {PACKAGE_PIN U1 IOSTANDARD LVCMOS33 IOB TRUE} [get_ports {cam_data[2]}]
set_property -dict {PACKAGE_PIN Y1 IOSTANDARD LVCMOS33 IOB TRUE} [get_ports {cam_data[3]}]
set_property -dict {PACKAGE_PIN AB1 IOSTANDARD LVCMOS33 IOB TRUE} [get_ports {cam_data[4]}]
set_property -dict {PACKAGE_PIN AA3 IOSTANDARD LVCMOS33 IOB TRUE} [get_ports {cam_data[5]}]
set_property -dict {PACKAGE_PIN AB3 IOSTANDARD LVCMOS33 IOB TRUE} [get_ports {cam_data[6]}]
set_property -dict {PACKAGE_PIN AA4 IOSTANDARD LVCMOS33 IOB TRUE} [get_ports {cam_data[7]}]
set_property -dict {PACKAGE_PIN AB7 IOSTANDARD LVCMOS33} [get_ports cam_vsync]
set_property -dict {PACKAGE_PIN AA5 IOSTANDARD LVCMOS33} [get_ports cam_href]
set_property -dict {PACKAGE_PIN AA6 IOSTANDARD LVCMOS33} [get_ports cam_scl]
set_property -dict {PACKAGE_PIN AB6 IOSTANDARD LVCMOS33} [get_ports cam_sda]
