TheSuperPixel/Embedded_Core_Boards/XC7A35T/测试例程/44_top_sd_rw/rtl/sd_ctrl_top.v

//****************************************Copyright (c)***********************************//
//原子哥在线教学平台：www.yuanzige.com
//技术支持：www.openedv.com
//淘宝店铺：http://openedv.taobao.com
//关注微信公众平台微信号："正点原子"，免费获取ZYNQ & FPGA & STM32 & LINUX资料。
//版权所有，盗版必究。
//Copyright(C) 正点原子 2018-2028
//All rights reserved
//----------------------------------------------------------------------------------------
// File name:           sd_ctrl_top
// Last modified Date:  2020/05/28 20:28:08
// Last Version:        V1.0
// Descriptions:        SD卡顶层控制模块
//                      
//----------------------------------------------------------------------------------------
// Created by:          正点原子
// Created date:        2020/05/28 20:28:08
// Version:             V1.0
// Descriptions:        The original version
//
//----------------------------------------------------------------------------------------
//****************************************************************************************//

module sd_ctrl_top(
    input                clk_ref       ,        //时钟信号
    input                clk_ref_180deg,  //时钟信号,与clk_ref相位相差180度
    input                rst_n         ,       //复位信号,低电平有效
    //SD卡接口
    input                   sd_miso      ,    //SD卡SPI串行输入数据信号
    output                 sd_clk         ,    //SD卡SPI时钟信号    
    output  reg          sd_cs          ,    //SD卡SPI片选信号
    output  reg          sd_mosi       ,   //SD卡SPI串行输出数据信号
    //用户写SD卡接口
    input                  wr_start_en    ,  //开始写SD卡数据信号
    input        [31:0]  wr_sec_addr   ,  //写数据扇区地址
    input        [15:0]  wr_data         ,  //写数据                  
    output                wr_busy         ,  //写数据忙信号
    output                wr_req          ,  //写数据请求信号    
    //用户读SD卡接口
    input                  rd_start_en     ,  //开始读SD卡数据信号
    input        [31:0]  rd_sec_addr   ,  //读数据扇区地址
    output                rd_busy         ,  //读数据忙信号
    output                rd_val_en       ,  //读数据有效信号
    output       [15:0] rd_val_data   ,   //读数据    
    
    output               sd_init_done     //SD卡初始化完成信号
    );

//wire define
wire                init_sd_clk   ;       //初始化SD卡时的低速时钟
wire                init_sd_cs    ;       //初始化模块SD片选信号
wire                init_sd_mosi  ;       //初始化模块SD数据输出信号
wire                wr_sd_cs      ;       //写数据模块SD片选信号     
wire                wr_sd_mosi    ;       //写数据模块SD数据输出信号 
wire                rd_sd_cs      ;       //读数据模块SD片选信号     
wire                rd_sd_mosi    ;       //读数据模块SD数据输出信号 

//*****************************************************
//**                    main code
//*****************************************************

//SD卡的SPI_CLK  
assign  sd_clk = (sd_init_done==1'b0)  ?  init_sd_clk  :  clk_ref_180deg;

//SD卡接口信号选择
always @(*) begin
    //SD卡初始化完成之前,端口信号和初始化模块信号相连
    if(sd_init_done == 1'b0) begin     
        sd_cs = init_sd_cs;
        sd_mosi = init_sd_mosi;
    end    
    else if(wr_busy) begin
        sd_cs = wr_sd_cs;
        sd_mosi = wr_sd_mosi;   
    end    
    else if(rd_busy) begin
        sd_cs = rd_sd_cs;
        sd_mosi = rd_sd_mosi;       
    end    
    else begin
        sd_cs = 1'b1;
        sd_mosi = 1'b1;
    end    
end    

//SD卡初始化
sd_init u_sd_init(
    .clk_ref            (clk_ref),
    .rst_n              (rst_n),
    
    .sd_miso            (sd_miso),
    .sd_clk             (init_sd_clk),
    .sd_cs              (init_sd_cs),
    .sd_mosi            (init_sd_mosi),
    
    .sd_init_done       (sd_init_done)
    );

//SD卡写数据
sd_write u_sd_write(
    .clk_ref            (clk_ref),
    .clk_ref_180deg     (clk_ref_180deg),
    .rst_n              (rst_n),
    
    .sd_miso            (sd_miso),
    .sd_cs              (wr_sd_cs),
    .sd_mosi            (wr_sd_mosi),
    //SD卡初始化完成之后响应写操作    
    .wr_start_en        (wr_start_en & sd_init_done),  
    .wr_sec_addr        (wr_sec_addr),
    .wr_data            (wr_data),
    .wr_busy            (wr_busy),
    .wr_req             (wr_req)
    );

//SD卡读数据
sd_read u_sd_read(
    .clk_ref            (clk_ref),
    .clk_ref_180deg     (clk_ref_180deg),
    .rst_n              (rst_n),
    
    .sd_miso            (sd_miso),
    .sd_cs              (rd_sd_cs),
    .sd_mosi            (rd_sd_mosi),    
    //SD卡初始化完成之后响应读操作
    .rd_start_en        (rd_start_en & sd_init_done),  
    .rd_sec_addr        (rd_sec_addr),
    .rd_busy            (rd_busy),
    .rd_val_en          (rd_val_en),
    .rd_val_data        (rd_val_data)
    );

endmodule
