TheSuperPixel/Embedded_Core_Boards/XC7A35T/测试例程/44_top_sd_rw/prj/top_sd_rw.srcs/constrs_1/new/pin.xdc

set_property PACKAGE_PIN R4 [get_ports sys_clk]
set_property PACKAGE_PIN U2 [get_ports sys_rst_n]
set_property IOSTANDARD LVCMOS33 [get_ports sys_clk]
set_property IOSTANDARD LVCMOS33 [get_ports sys_rst_n]

#SPI SD
set_property -dict {PACKAGE_PIN W4 IOSTANDARD LVCMOS33} [get_ports sd_miso]
set_property -dict {PACKAGE_PIN Y3 IOSTANDARD LVCMOS33} [get_ports sd_mosi]
set_property -dict {PACKAGE_PIN Y4 IOSTANDARD LVCMOS33} [get_ports sd_clk]
set_property -dict {PACKAGE_PIN Y2 IOSTANDARD LVCMOS33} [get_ports sd_cs]

#A7
set_property -dict {PACKAGE_PIN G22 IOSTANDARD LVCMOS33} [get_ports {led[0]}]
set_property -dict {PACKAGE_PIN G21 IOSTANDARD LVCMOS33} [get_ports {led[1]}]
set_property -dict {PACKAGE_PIN F21 IOSTANDARD LVCMOS33} [get_ports {led[2]}]
set_property -dict {PACKAGE_PIN B21 IOSTANDARD LVCMOS33} [get_ports {led[3]}]

set_property SLEW SLOW [get_ports {led[3]}]
set_property SLEW SLOW [get_ports {led[2]}]
set_property SLEW SLOW [get_ports {led[1]}]
set_property SLEW SLOW [get_ports {led[0]}]
set_property DRIVE 12 [get_ports {led[3]}]
set_property DRIVE 12 [get_ports {led[2]}]
set_property DRIVE 12 [get_ports {led[1]}]
set_property DRIVE 12 [get_ports {led[0]}]


set_property C_CLK_INPUT_FREQ_HZ 300000000 [get_debug_cores dbg_hub]
set_property C_ENABLE_CLK_DIVIDER false [get_debug_cores dbg_hub]
set_property C_USER_SCAN_CHAIN 1 [get_debug_cores dbg_hub]
