TheSuperPixel/Embedded_Core_Boards/XC7A35T/测试例程/0_led_twinkle/led_twinkle.srcs/constrs_1/new/led.xdc

#时序约束
create_clock -period 20.000 -name sys_clk -waveform {0.000 10.000} [get_ports sys_clk]

#IO管脚约束
set_property -dict {PACKAGE_PIN R4 IOSTANDARD LVCMOS33} [get_ports sys_clk]
set_property -dict {PACKAGE_PIN U2 IOSTANDARD LVCMOS33} [get_ports sys_rst_n]

#核心板LED
set_property -dict {PACKAGE_PIN F15 IOSTANDARD LVCMOS33} [get_ports led]

#固化
set_property CFGBVS VCCO [current_design]
set_property CONFIG_VOLTAGE 3.3 [current_design]
set_property BITSTREAM.GENERAL.COMPRESS true [current_design]
set_property BITSTREAM.CONFIG.CONFIGRATE 50 [current_design]
set_property BITSTREAM.CONFIG.SPI_BUSWIDTH 4 [current_design]
set_property BITSTREAM.CONFIG.SPI_FALL_EDGE Yes [current_design]
