TheSuperPixel/Embedded_Core_Boards/XC7A35T/测试例程/21_uart1_loopback/prj/uart_loopback.srcs/constrs_1/new/uart_loopback.xdc

#时序约束
create_clock -period 20.000 -name sys_clk [get_ports sys_clk]

#IO引脚约束
#----------------------系统时钟---------------------------
set_property -dict {PACKAGE_PIN R4 IOSTANDARD LVCMOS33} [get_ports sys_clk]

#----------------------系统复位---------------------------
set_property -dict {PACKAGE_PIN U2 IOSTANDARD LVCMOS33} [get_ports sys_rst_n]

#----------------------USB UART---------------------------
set_property -dict {PACKAGE_PIN U3 IOSTANDARD LVCMOS33} [get_ports uart_rxd]
set_property -dict {PACKAGE_PIN V3 IOSTANDARD LVCMOS33} [get_ports uart_txd]
