TheSuperPixel/Embedded_Core_Boards/STM32H750/测试例程/彩色液晶屏驱动-基于1.69寸240x280分辨率/Drivers/User/Src/lcd_spi_169.c

 /***
	************************************************************************************************************************************************************************************************
	*	@version V1.0
	*  @date    2024-4-17
	*	@author  反客科技
   **********************************************************************************************************************************************************************************************
   *  @description
	*
	*	实验平台：反客STM32H750XBH6核心板 （型号：FK750M6-XBH6）+ 1.69寸液晶模块（型号：SPI169M1-240*280） 
	*	淘宝地址：https://shop212360197.taobao.com
	*	QQ交流群：536665479
	*
>>>>> 重要说明：
	*
	*  1.屏幕配置为16位RGB565格式
	*  2.SPI通信速度为60M
   *
>>>>> 其他说明：
	*
	*	1. 中文字库使用的是小字库，即用到了对应的汉字再去取模，用户可以根据需求自行增添或删减
	*	2. 各个函数的功能和使用可以参考函数的说明
	*
	*********************************************************************************************************************************************************************************************FANKE*****
***/

#include "lcd_spi_169.h"

extern	SPI_HandleTypeDef hspi6;	      // SPI_HandleTypeDef 结构体变量

#define  LCD_SPI hspi6           // SPI局部宏，方便修改和移植

static pFONT *LCD_AsciiFonts;		// 英文字体，ASCII字符集
static pFONT *LCD_CHFonts;		   // 中文字体（同时也包含英文字体）

// 因为这类SPI的屏幕，每次更新显示时，需要先配置坐标区域、再写显存，
// 在显示字符时，如果是一个个点去写坐标写显存，会非常慢，
// 因此开辟一片缓冲区，先将需要显示的数据写进缓冲区，最后再批量写入显存。
// 用户可以根据实际情况去修改此处缓冲区的大小，
// 例如，用户需要显示32*32的汉字时，需要的大小为 32*32*2 = 2048 字节（每个像素点占2字节）
uint16_t  LCD_Buff[1024];        // LCD缓冲区，16位宽（每个像素点占2字节）

struct	//LCD相关参数结构体
{
	uint32_t Color;  				//	LCD当前画笔颜色
	uint32_t BackColor;			//	背景色
   uint8_t  ShowNum_Mode;		// 数字显示模式
	uint8_t  Direction;			//	显示方向
   uint16_t Width;            // 屏幕像素长度
   uint16_t Height;           // 屏幕像素宽度	
   uint8_t  X_Offset;         // X坐标偏移，用于设置屏幕控制器的显存写入方式
   uint8_t  Y_Offset;         // Y坐标偏移，用于设置屏幕控制器的显存写入方式
}LCD;

// 该函数修改于HAL的SPI库函数，专为 LCD_Clear() 清屏函数修改，
// 目的是为了SPI传输数据不限数据长度的写入
HAL_StatusTypeDef LCD_SPI_Transmit(SPI_HandleTypeDef *hspi, uint16_t pData, uint32_t Size);
HAL_StatusTypeDef LCD_SPI_TransmitBuffer (SPI_HandleTypeDef *hspi, uint16_t *pData, uint32_t Size);

/****************************************************************************************************************************************
*	函 数 名:	LCD_GPIO_Init
*	
*	函数功能:	初始化 背光 引脚 、 数据指令选择 引脚
****************************************************************************************************************************************/

void LCD_GPIO_Init(void)
{
   GPIO_InitTypeDef GPIO_InitStruct = {0};

	
	GPIO_LDC_Backlight_CLK_ENABLE;   // 使能 背光        引脚时钟
	GPIO_LDC_DC_CLK_ENABLE;          // 使能 数据指令选择 引脚时钟

/******************************************************  

	PH6     ------> 背光  引脚
	PJ11    ------> 数据指令选择 引脚
	
*******************************************************/


 
// 初始化 背光 引脚  
	GPIO_InitStruct.Pin 		= LCD_Backlight_PIN;				// 背光 引脚
	GPIO_InitStruct.Mode 	= GPIO_MODE_OUTPUT_PP;			// 推挽输出模式
	GPIO_InitStruct.Pull 	= GPIO_NOPULL;						// 无上下拉
	GPIO_InitStruct.Speed 	= GPIO_SPEED_FREQ_LOW;			// 速度等级低
	HAL_GPIO_Init(LCD_Backlight_PORT, &GPIO_InitStruct);	// 初始化  

// 初始化 数据指令选择 引脚  
	GPIO_InitStruct.Pin 		= LCD_DC_PIN;				      // 数据指令选择 引脚
	GPIO_InitStruct.Mode 	= GPIO_MODE_OUTPUT_PP;			// 推挽输出模式
	GPIO_InitStruct.Pull 	= GPIO_NOPULL;						// 无上下拉
	GPIO_InitStruct.Speed 	= GPIO_SPEED_FREQ_LOW;			// 速度等级低
	HAL_GPIO_Init(LCD_DC_PORT, &GPIO_InitStruct);	      // 初始化  

}


/****************************************************************************************************************************************
*	函 数 名: LCD_WriteCommand
*
*	入口参数: lcd_command - 需要写入的控制指令
*
*	函数功能: 用于向屏幕控制器写入指令
*
****************************************************************************************************************************************/

void  LCD_WriteCommand(uint8_t lcd_command)
{
   LCD_DC_Command;     // 数据指令选择 引脚输出低电平，代表本次传输 指令

   HAL_SPI_Transmit(&LCD_SPI, &lcd_command, 1, 1000); // 启动SPI传输
}

/****************************************************************************************************************************************
*	函 数 名: LCD_WriteData_8bit
*
*	入口参数: lcd_data - 需要写入的数据，8位
*
*	函数功能: 写入8位数据
*	
****************************************************************************************************************************************/

void  LCD_WriteData_8bit(uint8_t lcd_data)
{
   LCD_DC_Data;     // 数据指令选择 引脚输出高电平，代表本次传输 数据

   HAL_SPI_Transmit(&LCD_SPI, &lcd_data, 1, 1000) ; // 启动SPI传输
}

/****************************************************************************************************************************************
*	函 数 名: LCD_WriteData_16bit
*
*	入口参数: lcd_data - 需要写入的数据，16位
*
*	函数功能: 写入16位数据
*	
****************************************************************************************************************************************/

void  LCD_WriteData_16bit(uint16_t lcd_data)
{
   uint8_t lcd_data_buff[2];    // 数据发送区
   LCD_DC_Data;      // 数据指令选择 引脚输出高电平，代表本次传输 数据
 
   lcd_data_buff[0] = lcd_data>>8;  // 将数据拆分
   lcd_data_buff[1] = lcd_data;
		
	HAL_SPI_Transmit(&LCD_SPI, lcd_data_buff, 2, 1000) ;   // 启动SPI传输
}

/****************************************************************************************************************************************
*	函 数 名: LCD_WriteBuff
*
*	入口参数: DataBuff - 数据区，DataSize - 数据长度
*
*	函数功能: 批量写入数据到屏幕
*	
****************************************************************************************************************************************/

void  LCD_WriteBuff(uint16_t *DataBuff, uint16_t DataSize)
{
	LCD_DC_Data;     // 数据指令选择 引脚输出高电平，代表本次传输 数据	

// 修改为16位数据宽度，写入数据更加效率，不需要拆分	
   LCD_SPI.Init.DataSize 	= SPI_DATASIZE_16BIT;   //	16位数据宽度
   HAL_SPI_Init(&LCD_SPI);		
	
	HAL_SPI_Transmit(&LCD_SPI, (uint8_t *)DataBuff, DataSize, 1000) ; // 启动SPI传输
	
// 改回8位数据宽度，因为指令和部分数据都是按照8位传输的
	LCD_SPI.Init.DataSize 	= SPI_DATASIZE_8BIT;    //	8位数据宽度
   HAL_SPI_Init(&LCD_SPI);	
}

/****************************************************************************************************************************************
*	函 数 名: SPI_LCD_Init
*
*	函数功能: 初始化屏幕控制器的各种参数
*	
****************************************************************************************************************************************/

void SPI_LCD_Init(void)
{
   LCD_GPIO_Init();               // 初始化 背光 引脚 、 数据指令选择 引脚
   
   HAL_Delay(10);               	// 屏幕刚完成复位时（包括上电复位），需要等待至少5ms才能发送指令
 	LCD_WriteCommand(0x36);       // 显存访问控制 指令，用于设置访问显存的方式
	LCD_WriteData_8bit(0x00);     // 配置成 从上到下、从左到右，RGB像素格式

	LCD_WriteCommand(0x3A);			// 接口像素格式 指令，用于设置使用 12位、16位还是18位色
	LCD_WriteData_8bit(0x05);     // 此处配置成 16位 像素格式

// 接下来很多都是电压设置指令，直接使用厂家给设定值
 	LCD_WriteCommand(0xB2);			
	LCD_WriteData_8bit(0x0C);
	LCD_WriteData_8bit(0x0C); 
	LCD_WriteData_8bit(0x00); 
	LCD_WriteData_8bit(0x33); 
	LCD_WriteData_8bit(0x33); 			

	LCD_WriteCommand(0xB7);		   // 栅极电压设置指令	
	LCD_WriteData_8bit(0x35);     // VGH = 13.26V，VGL = -10.43V

	LCD_WriteCommand(0xBB);			// 公共电压设置指令
	LCD_WriteData_8bit(0x19);     // VCOM = 1.35V

	LCD_WriteCommand(0xC0);
	LCD_WriteData_8bit(0x2C);

	LCD_WriteCommand(0xC2);       // VDV 和 VRH 来源设置
	LCD_WriteData_8bit(0x01);     // VDV 和 VRH 由用户自由配置

	LCD_WriteCommand(0xC3);			// VRH电压 设置指令  
	LCD_WriteData_8bit(0x12);     // VRH电压 = 4.6+( vcom+vcom offset+vdv)
				
	LCD_WriteCommand(0xC4);		   // VDV电压 设置指令	
	LCD_WriteData_8bit(0x20);     // VDV电压 = 0v

	LCD_WriteCommand(0xC6); 		// 正常模式的帧率控制指令
	LCD_WriteData_8bit(0x0F);   	// 设置屏幕控制器的刷新帧率为60帧    

	LCD_WriteCommand(0xD0);			// 电源控制指令
	LCD_WriteData_8bit(0xA4);     // 无效数据，固定写入0xA4
	LCD_WriteData_8bit(0xA1);     // AVDD = 6.8V ，AVDD = -4.8V ，VDS = 2.3V

	LCD_WriteCommand(0xE0);       // 正极电压伽马值设定
	LCD_WriteData_8bit(0xD0);
	LCD_WriteData_8bit(0x04);
	LCD_WriteData_8bit(0x0D);
	LCD_WriteData_8bit(0x11);
	LCD_WriteData_8bit(0x13);
	LCD_WriteData_8bit(0x2B);
	LCD_WriteData_8bit(0x3F);
	LCD_WriteData_8bit(0x54);
	LCD_WriteData_8bit(0x4C);
	LCD_WriteData_8bit(0x18);
	LCD_WriteData_8bit(0x0D);
	LCD_WriteData_8bit(0x0B);
	LCD_WriteData_8bit(0x1F);
	LCD_WriteData_8bit(0x23);

	LCD_WriteCommand(0xE1);      // 负极电压伽马值设定
	LCD_WriteData_8bit(0xD0);
	LCD_WriteData_8bit(0x04);
	LCD_WriteData_8bit(0x0C);
	LCD_WriteData_8bit(0x11);
	LCD_WriteData_8bit(0x13);
	LCD_WriteData_8bit(0x2C);
	LCD_WriteData_8bit(0x3F);
	LCD_WriteData_8bit(0x44);
	LCD_WriteData_8bit(0x51);
	LCD_WriteData_8bit(0x2F);
	LCD_WriteData_8bit(0x1F);
	LCD_WriteData_8bit(0x1F);
	LCD_WriteData_8bit(0x20);
	LCD_WriteData_8bit(0x23);

	LCD_WriteCommand(0x21);       // 打开反显，因为面板是常黑型，操作需要反过来

 // 退出休眠指令，LCD控制器在刚上电、复位时，会自动进入休眠模式 ，因此操作屏幕之前，需要退出休眠  
	LCD_WriteCommand(0x11);       // 退出休眠 指令
   HAL_Delay(120);               // 需要等待120ms，让电源电压和时钟电路稳定下来

 // 打开显示指令，LCD控制器在刚上电、复位时，会自动关闭显示 
	LCD_WriteCommand(0x29);       // 打开显示   	
	
// 以下进行一些驱动的默认设置
   LCD_SetDirection(Direction_V);  	      //	设置显示方向
	LCD_SetBackColor(LCD_BLACK);           // 设置背景色
 	LCD_SetColor(LCD_WHITE);               // 设置画笔色  
	LCD_Clear();                           // 清屏

   LCD_SetAsciiFont(&ASCII_Font24);       // 设置默认字体
   LCD_ShowNumMode(Fill_Zero);	      	// 设置变量显示模式，多余位填充空格还是填充0

// 全部设置完毕之后，打开背光	
   LCD_Backlight_ON;  // 引脚输出高电平点亮背光
}

/****************************************************************************************************************************************
*	函 数 名:	 LCD_SetAddress
*
*	入口参数:	 x1 - 起始水平坐标   y1 - 起始垂直坐标  
*              x2 - 终点水平坐标   y2 - 终点垂直坐标	   
*	
*	函数功能:   设置需要显示的坐标区域		 			 
*****************************************************************************************************************************************/

void LCD_SetAddress(uint16_t x1,uint16_t y1,uint16_t x2,uint16_t y2)		
{
	LCD_WriteCommand(0x2a);			//	列地址设置，即X坐标
	LCD_WriteData_16bit(x1+LCD.X_Offset);
	LCD_WriteData_16bit(x2+LCD.X_Offset);

	LCD_WriteCommand(0x2b);			//	行地址设置，即Y坐标
	LCD_WriteData_16bit(y1+LCD.Y_Offset);
	LCD_WriteData_16bit(y2+LCD.Y_Offset);

	LCD_WriteCommand(0x2c);			//	开始写入显存，即要显示的颜色数据
}

/****************************************************************************************************************************************
*	函 数 名:	LCD_SetColor
*
*	入口参数:	Color - 要显示的颜色，示例：0x0000FF 表示蓝色
*
*	函数功能:	此函数用于设置画笔的颜色，例如显示字符、画点画线、绘图的颜色
*
*	说    明:	1. 为了方便用户使用自定义颜色，入口参数 Color 使用24位 RGB888的颜色格式，用户无需关心颜色格式的转换
*					2. 24位的颜色中，从高位到低位分别对应 R、G、B  3个颜色通道
*
*****************************************************************************************************************************************/

void LCD_SetColor(uint32_t Color)
{
	uint16_t Red_Value = 0, Green_Value = 0, Blue_Value = 0; //各个颜色通道的值

	Red_Value   = (uint16_t)((Color&0x00F80000)>>8);   // 转换成 16位 的RGB565颜色
	Green_Value = (uint16_t)((Color&0x0000FC00)>>5);
	Blue_Value  = (uint16_t)((Color&0x000000F8)>>3);

	LCD.Color = (uint16_t)(Red_Value | Green_Value | Blue_Value);  // 将颜色写入全局LCD参数		
}

/****************************************************************************************************************************************
*	函 数 名:	LCD_SetBackColor
*
*	入口参数:	Color - 要显示的颜色，示例：0x0000FF 表示蓝色
*
*	函数功能:	设置背景色,此函数用于清屏以及显示字符的背景色
*
*	说    明:	1. 为了方便用户使用自定义颜色，入口参数 Color 使用24位 RGB888的颜色格式，用户无需关心颜色格式的转换
*					2. 24位的颜色中，从高位到低位分别对应 R、G、B  3个颜色通道
*
*****************************************************************************************************************************************/

void LCD_SetBackColor(uint32_t Color)
{
	uint16_t Red_Value = 0, Green_Value = 0, Blue_Value = 0; //各个颜色通道的值

	Red_Value   = (uint16_t)((Color&0x00F80000)>>8);   // 转换成 16位 的RGB565颜色
	Green_Value = (uint16_t)((Color&0x0000FC00)>>5);
	Blue_Value  = (uint16_t)((Color&0x000000F8)>>3);

	LCD.BackColor = (uint16_t)(Red_Value | Green_Value | Blue_Value);	// 将颜色写入全局LCD参数			   	
}

/****************************************************************************************************************************************
*	函 数 名:	LCD_SetDirection
*
*	入口参数:	direction - 要显示的方向
*
*	函数功能:	设置要显示的方向
*
*	说    明:   1. 可输入参数 Direction_H 、Direction_V 、Direction_H_Flip 、Direction_V_Flip        
*              2. 使用示例 LCD_DisplayDirection(Direction_H) ，即设置屏幕横屏显示
*
*****************************************************************************************************************************************/

void LCD_SetDirection(uint8_t direction)
{
	LCD.Direction = direction;    // 写入全局LCD参数

   if( direction == Direction_H )   // 横屏显示
   {
      LCD_WriteCommand(0x36);    		// 显存访问控制 指令，用于设置访问显存的方式
      LCD_WriteData_8bit(0x70);        // 横屏显示
      LCD.X_Offset   = 20;             // 设置控制器坐标偏移量
      LCD.Y_Offset   = 0;   
      LCD.Width      = LCD_Height;		// 重新赋值长、宽
      LCD.Height     = LCD_Width;		
   }
   else if( direction == Direction_V )
   {
      LCD_WriteCommand(0x36);    		// 显存访问控制 指令，用于设置访问显存的方式
      LCD_WriteData_8bit(0x00);        // 垂直显示
      LCD.X_Offset   = 0;              // 设置控制器坐标偏移量
      LCD.Y_Offset   = 20;     
      LCD.Width      = LCD_Width;		// 重新赋值长、宽
      LCD.Height     = LCD_Height;						
   }
   else if( direction == Direction_H_Flip )
   {
      LCD_WriteCommand(0x36);   			 // 显存访问控制 指令，用于设置访问显存的方式
      LCD_WriteData_8bit(0xA0);         // 横屏显示，并上下翻转，RGB像素格式
      LCD.X_Offset   = 20;              // 设置控制器坐标偏移量
      LCD.Y_Offset   = 0;      
      LCD.Width      = LCD_Height;		 // 重新赋值长、宽
      LCD.Height     = LCD_Width;				
   }
   else if( direction == Direction_V_Flip )
   {
      LCD_WriteCommand(0x36);    		// 显存访问控制 指令，用于设置访问显存的方式
      LCD_WriteData_8bit(0xC0);        // 垂直显示 ，并上下翻转，RGB像素格式
      LCD.X_Offset   = 0;              // 设置控制器坐标偏移量
      LCD.Y_Offset   = 20;     
      LCD.Width      = LCD_Width;		// 重新赋值长、宽
      LCD.Height     = LCD_Height;				
   }   
}

/****************************************************************************************************************************************
*	函 数 名:	LCD_SetAsciiFont
*
*	入口参数:	*fonts - 要设置的ASCII字体
*
*	函数功能:	设置ASCII字体，可选择使用 3216/2412/2010/1608/1206 五种大小的字体
*
*	说    明:	1. 使用示例 LCD_SetAsciiFont(&ASCII_Font24) ，即设置 2412的 ASCII字体
*					2. 相关字模存放在 lcd_fonts.c 			
*
*****************************************************************************************************************************************/

void LCD_SetAsciiFont(pFONT *Asciifonts)
{
  LCD_AsciiFonts = Asciifonts;
}

/****************************************************************************************************************************************
*	函 数 名:	LCD_Clear
*
*	函数功能:	清屏函数，将LCD清除为 LCD.BackColor 的颜色
*
*	说    明:	先用 LCD_SetBackColor() 设置要清除的背景色，再调用该函数清屏即可
*
*****************************************************************************************************************************************/

void LCD_Clear(void)
{
   LCD_SetAddress(0,0,LCD.Width-1,LCD.Height-1);	// 设置坐标
	
	LCD_DC_Data;     // 数据指令选择 引脚输出高电平，代表本次传输 数据	

// 修改为16位数据宽度，写入数据更加效率，不需要拆分	
   LCD_SPI.Init.DataSize 	= SPI_DATASIZE_16BIT;   //	16位数据宽度
   HAL_SPI_Init(&LCD_SPI);		
	
   LCD_SPI_Transmit(&LCD_SPI, LCD.BackColor, LCD.Width * LCD.Height) ;   // 启动传输

// 改回8位数据宽度，因为指令和部分数据都是按照8位传输的
	LCD_SPI.Init.DataSize 	= SPI_DATASIZE_8BIT;    //	8位数据宽度
   HAL_SPI_Init(&LCD_SPI);
}

/****************************************************************************************************************************************
*	函 数 名:	LCD_ClearRect
*
*	入口参数:	x - 起始水平坐标
*					y - 起始垂直坐标
*					width  - 要清除区域的横向长度
*					height - 要清除区域的纵向宽度
*
*	函数功能:	局部清屏函数，将指定位置对应的区域清除为 LCD.BackColor 的颜色
*
*	说    明:	1. 先用 LCD_SetBackColor() 设置要清除的背景色，再调用该函数清屏即可
*				   2. 使用示例 LCD_ClearRect( 10, 10, 100, 50) ，清除坐标(10,10)开始的长100宽50的区域
*
*****************************************************************************************************************************************/

void LCD_ClearRect(uint16_t x, uint16_t y, uint16_t width, uint16_t height)
{
   LCD_SetAddress( x, y, x+width-1, y+height-1);	// 设置坐标	
	
	LCD_DC_Data;     // 数据指令选择 引脚输出高电平，代表本次传输 数据	

// 修改为16位数据宽度，写入数据更加效率，不需要拆分	
   LCD_SPI.Init.DataSize 	= SPI_DATASIZE_16BIT;   //	16位数据宽度
   HAL_SPI_Init(&LCD_SPI);		
	
   LCD_SPI_Transmit(&LCD_SPI, LCD.BackColor, width*height) ;  // 启动传输

// 改回8位数据宽度，因为指令和部分数据都是按照8位传输的
	LCD_SPI.Init.DataSize 	= SPI_DATASIZE_8BIT;    //	8位数据宽度
   HAL_SPI_Init(&LCD_SPI);

}

/****************************************************************************************************************************************
*	函 数 名:	LCD_DrawPoint
*
*	入口参数:	x - 起始水平坐标
*					y - 起始垂直坐标
*					color  - 要绘制的颜色，使用 24位 RGB888 的颜色格式，用户无需关心颜色格式的转换
*
*	函数功能:	在指定坐标绘制指定颜色的点
*
*	说    明:	使用示例 LCD_DrawPoint( 10, 10, 0x0000FF) ，在坐标(10,10)绘制蓝色的点
*
*****************************************************************************************************************************************/

void LCD_DrawPoint(uint16_t x,uint16_t y,uint32_t color)
{
	LCD_SetAddress(x,y,x,y);	//	设置坐标 

	LCD_WriteData_16bit(color)	;
}

/****************************************************************************************************************************************
*	函 数 名:	LCD_DisplayChar
*
*	入口参数:	x - 起始水平坐标
*					y - 起始垂直坐标
*					c  - ASCII字符
*
*	函数功能:	在指定坐标显示指定的字符
*
*	说    明:	1. 可设置要显示的字体，例如使用 LCD_SetAsciiFont(&ASCII_Font24) 设置为 2412的ASCII字体
*					2.	可设置要显示的颜色，例如使用 LCD_SetColor(0xff0000FF) 设置为蓝色
*					3. 可设置对应的背景色，例如使用 LCD_SetBackColor(0x000000) 设置为黑色的背景色
*					4. 使用示例 LCD_DisplayChar( 10, 10, 'a') ，在坐标(10,10)显示字符 'a'
*
*****************************************************************************************************************************************/

void LCD_DisplayChar(uint16_t x, uint16_t y,uint8_t c)
{
	uint16_t  index = 0, counter = 0 ,i = 0, w = 0;		// 计数变量
   uint8_t   disChar;		//存储字符的地址

	c = c - 32; 	// 计算ASCII字符的偏移

	for(index = 0; index < LCD_AsciiFonts->Sizes; index++)	
	{
		disChar = LCD_AsciiFonts->pTable[c*LCD_AsciiFonts->Sizes + index]; //获取字符的模值
		for(counter = 0; counter < 8; counter++)
		{ 
			if(disChar & 0x01)	
			{		
            LCD_Buff[i] =  LCD.Color;			// 当前模值不为0时，使用画笔色绘点
			}
			else		
			{		
            LCD_Buff[i] = LCD.BackColor;		//否则使用背景色绘制点
			}
			disChar >>= 1;
			i++;
         w++;
 			if( w == LCD_AsciiFonts->Width ) // 如果写入的数据达到了字符宽度，则退出当前循环
			{								   // 进入下一字符的写入的绘制
				w = 0;
				break;
			}        
		}	
	}		
   LCD_SetAddress( x, y, x+LCD_AsciiFonts->Width-1, y+LCD_AsciiFonts->Height-1);	   // 设置坐标	
   LCD_WriteBuff(LCD_Buff,LCD_AsciiFonts->Width*LCD_AsciiFonts->Height);          // 写入显存
}

/****************************************************************************************************************************************
*	函 数 名:	LCD_DisplayString
*
*	入口参数:	x - 起始水平坐标
*					y - 起始垂直坐标
*					p - ASCII字符串的首地址
*
*	函数功能:	在指定坐标显示指定的字符串
*
*	说    明:	1. 可设置要显示的字体，例如使用 LCD_SetAsciiFont(&ASCII_Font24) 设置为 2412的ASCII字体
*					2.	可设置要显示的颜色，例如使用 LCD_SetColor(0x0000FF) 设置为蓝色
*					3. 可设置对应的背景色，例如使用 LCD_SetBackColor(0x000000) 设置为黑色的背景色
*					4. 使用示例 LCD_DisplayString( 10, 10, "FANKE") ，在起始坐标为(10,10)的地方显示字符串"FANKE"
*
*****************************************************************************************************************************************/

void LCD_DisplayString( uint16_t x, uint16_t y, char *p) 
{  
	while ((x < LCD.Width) && (*p != 0))	//判断显示坐标是否超出显示区域并且字符是否为空字符
	{
		 LCD_DisplayChar( x,y,*p);
		 x += LCD_AsciiFonts->Width; //显示下一个字符
		 p++;	//取下一个字符地址
	}
}

/****************************************************************************************************************************************
*	函 数 名:	LCD_SetTextFont
*
*	入口参数:	*fonts - 要设置的文本字体
*
*	函数功能:	设置文本字体，包括中文和ASCII字符，
*
*	说    明:	1. 可选择使用 3232/2424/2020/1616/1212 五种大小的中文字体，
*						并且对应的设置ASCII字体为 3216/2412/2010/1608/1206
*					2. 相关字模存放在 lcd_fonts.c 
*					3. 中文字库使用的是小字库，即用到了对应的汉字再去取模
*					4. 使用示例 LCD_SetTextFont(&CH_Font24) ，即设置 2424的中文字体以及2412的ASCII字符字体
*
*****************************************************************************************************************************************/

void LCD_SetTextFont(pFONT *fonts)
{
	LCD_CHFonts = fonts;		// 设置中文字体
	switch(fonts->Width )
	{
		case 12:	LCD_AsciiFonts = &ASCII_Font12;	break;	// 设置ASCII字符的字体为 1206
		case 16:	LCD_AsciiFonts = &ASCII_Font16;	break;	// 设置ASCII字符的字体为 1608
		case 20:	LCD_AsciiFonts = &ASCII_Font20;	break;	// 设置ASCII字符的字体为 2010	
		case 24:	LCD_AsciiFonts = &ASCII_Font24;	break;	// 设置ASCII字符的字体为 2412
		case 32:	LCD_AsciiFonts = &ASCII_Font32;	break;	// 设置ASCII字符的字体为 3216		
		default: break;
	}
}
/******************************************************************************************************************************************
*	函 数 名:	LCD_DisplayChinese
*
*	入口参数:	x - 起始水平坐标
*					y - 起始垂直坐标
*					pText - 中文字符
*
*	函数功能:	在指定坐标显示指定的单个中文字符
*
*	说    明:	1. 可设置要显示的字体，例如使用 LCD_SetTextFont(&CH_Font24) 设置为 2424的中文字体以及2412的ASCII字符字体
*					2.	可设置要显示的颜色，例如使用 LCD_SetColor(0xff0000FF) 设置为蓝色
*					3. 可设置对应的背景色，例如使用 LCD_SetBackColor(0xff000000) 设置为黑色的背景色
*					4. 使用示例 LCD_DisplayChinese( 10, 10, "反") ，在坐标(10,10)显示中文字符"反"
*
*****************************************************************************************************************************************/

void LCD_DisplayChinese(uint16_t x, uint16_t y, char *pText) 
{
	uint16_t  i=0,index = 0, counter = 0;	// 计数变量
	uint16_t  addr;	// 字模地址
   uint8_t   disChar;	//字模的值
	uint16_t  Xaddress = 0; //水平坐标

	while(1)
	{		
		// 对比数组中的汉字编码，用以定位该汉字字模的地址		
		if ( *(LCD_CHFonts->pTable + (i+1)*LCD_CHFonts->Sizes + 0)==*pText && *(LCD_CHFonts->pTable + (i+1)*LCD_CHFonts->Sizes + 1)==*(pText+1) )	
		{   
			addr=i;	// 字模地址偏移
			break;
		}				
		i+=2;	// 每个中文字符编码占两字节

		if(i >= LCD_CHFonts->Table_Rows)	break;	// 字模列表中无相应的汉字	
	}	
	i=0;
	for(index = 0; index <LCD_CHFonts->Sizes; index++)
	{	
		disChar = *(LCD_CHFonts->pTable + (addr)*LCD_CHFonts->Sizes + index);	// 获取相应的字模地址
		
		for(counter = 0; counter < 8; counter++)
		{ 
			if(disChar & 0x01)	
			{		
            LCD_Buff[i] =  LCD.Color;			// 当前模值不为0时，使用画笔色绘点
			}
			else		
			{		
            LCD_Buff[i] = LCD.BackColor;		// 否则使用背景色绘制点
			}
         i++;
			disChar >>= 1;
			Xaddress++;  //水平坐标自加
			
			if( Xaddress == LCD_CHFonts->Width ) 	//	如果水平坐标达到了字符宽度，则退出当前循环
			{														//	进入下一行的绘制
				Xaddress = 0;
				break;
			}
		}	
	}	
   LCD_SetAddress( x, y, x+LCD_CHFonts->Width-1, y+LCD_CHFonts->Height-1);	   // 设置坐标	
   LCD_WriteBuff(LCD_Buff,LCD_CHFonts->Width*LCD_CHFonts->Height);            // 写入显存
}

/*****************************************************************************************************************************************
*	函 数 名:	LCD_DisplayText
*
*	入口参数:	x - 起始水平坐标
*					y - 起始垂直坐标
*					pText - 字符串，可以显示中文或者ASCII字符
*
*	函数功能:	在指定坐标显示指定的字符串
*
*	说    明:	1. 可设置要显示的字体，例如使用 LCD_SetTextFont(&CH_Font24) 设置为 2424的中文字体以及2412的ASCII字符字体
*					2.	可设置要显示的颜色，例如使用 LCD_SetColor(0xff0000FF) 设置为蓝色
*					3. 可设置对应的背景色，例如使用 LCD_SetBackColor(0xff000000) 设置为黑色的背景色
*					4. 使用示例 LCD_DisplayChinese( 10, 10, "反客科技STM32") ，在坐标(10,10)显示字符串"反客科技STM32"
*
**********************************************************************************************************************************fanke*******/

void LCD_DisplayText(uint16_t x, uint16_t y, char *pText) 
{  
 	
	while(*pText != 0)	// 判断是否为空字符
	{
		if(*pText<=0x7F)	// 判断是否为ASCII码
		{
			LCD_DisplayChar(x,y,*pText);	// 显示ASCII
			x+=LCD_AsciiFonts->Width;				// 水平坐标调到下一个字符处
			pText++;								// 字符串地址+1
		}
		else					// 若字符为汉字
		{			
			LCD_DisplayChinese(x,y,pText);	// 显示汉字
			x+=LCD_CHFonts->Width;				// 水平坐标调到下一个字符处
			pText+=2;								// 字符串地址+2，汉字的编码要2字节
		}
	}	
}

/*****************************************************************************************************************************************
*	函 数 名:	LCD_ShowNumMode
*
*	入口参数:	mode - 设置变量的显示模式
*
*	函数功能:	设置变量显示时多余位补0还是补空格，可输入参数 Fill_Space 填充空格，Fill_Zero 填充零
*
*	说    明:   1. 只有 LCD_DisplayNumber() 显示整数 和 LCD_DisplayDecimals()显示小数 这两个函数用到
*					2. 使用示例 LCD_ShowNumMode(Fill_Zero) 设置多余位填充0，例如 123 可以显示为 000123
*
*****************************************************************************************************************************************/

void LCD_ShowNumMode(uint8_t mode)
{
	LCD.ShowNum_Mode = mode;
}

/*****************************************************************************************************************************************
*	函 数 名:	LCD_DisplayNumber
*
*	入口参数:	x - 起始水平坐标
*					y - 起始垂直坐标
*					number - 要显示的数字,范围在 -2147483648~2147483647 之间
*					len - 数字的位数，如果位数超过len，将按其实际长度输出，如果需要显示负数，请预留一个位的符号显示空间
*
*	函数功能:	在指定坐标显示指定的整数变量
*
*	说    明:	1. 可设置要显示的字体，例如使用 LCD_SetAsciiFont(&ASCII_Font24) 设置为的ASCII字符字体
*					2.	可设置要显示的颜色，例如使用 LCD_SetColor(0x0000FF) 设置为蓝色
*					3. 可设置对应的背景色，例如使用 LCD_SetBackColor(0x000000) 设置为黑色的背景色
*					4. 使用示例 LCD_DisplayNumber( 10, 10, a, 5) ，在坐标(10,10)显示指定变量a,总共5位，多余位补0或空格，
*						例如 a=123 时，会根据 LCD_ShowNumMode()的设置来显示  123(前面两个空格位) 或者00123
*						
*****************************************************************************************************************************************/

void  LCD_DisplayNumber( uint16_t x, uint16_t y, int32_t number, uint8_t len) 
{  
	char   Number_Buffer[15];				// 用于存储转换后的字符串

	if( LCD.ShowNum_Mode == Fill_Zero)	// 多余位补0
	{
		sprintf( Number_Buffer , "%0.*d",len, number );	// 将 number 转换成字符串，便于显示		
	}
	else			// 多余位补空格
	{	
		sprintf( Number_Buffer , "%*d",len, number );	// 将 number 转换成字符串，便于显示		
	}
	
	LCD_DisplayString( x, y,(char *)Number_Buffer) ;  // 将转换得到的字符串显示出来
	
}

/***************************************************************************************************************************************
*	函 数 名:	LCD_DisplayDecimals
*
*	入口参数:	x - 起始水平坐标
*					y - 起始垂直坐标
*					decimals - 要显示的数字, double型取值1.7 x 10^（-308）~ 1.7 x 10^（+308），但是能确保准确的有效位数为15~16位
*
*       			len - 整个变量的总位数（包括小数点和负号），若实际的总位数超过了指定的总位数，将按实际的总长度位输出，
*							示例1：小数 -123.123 ，指定 len <=8 的话，则实际照常输出 -123.123
*							示例2：小数 -123.123 ，指定 len =10 的话，则实际输出   -123.123(负号前面会有两个空格位) 
*							示例3：小数 -123.123 ，指定 len =10 的话，当调用函数 LCD_ShowNumMode() 设置为填充0模式时，实际输出 -00123.123 
*
*					decs - 要保留的小数位数，若小数的实际位数超过了指定的小数位，则按指定的宽度四舍五入输出
*							 示例：1.12345 ，指定 decs 为4位的话，则输出结果为1.1235
*
*	函数功能:	在指定坐标显示指定的变量，包括小数
*
*	说    明:	1. 可设置要显示的字体，例如使用 LCD_SetAsciiFont(&ASCII_Font24) 设置为的ASCII字符字体
*					2.	可设置要显示的颜色，例如使用 LCD_SetColor(0x0000FF) 设置为蓝色
*					3. 可设置对应的背景色，例如使用 LCD_SetBackColor(0x000000) 设置为黑色的背景色
*					4. 使用示例 LCD_DisplayDecimals( 10, 10, a, 5, 3) ，在坐标(10,10)显示字变量a,总长度为5位，其中保留3位小数
*						
*****************************************************************************************************************************************/

void  LCD_DisplayDecimals( uint16_t x, uint16_t y, double decimals, uint8_t len, uint8_t decs) 
{  
	char  Number_Buffer[20];				// 用于存储转换后的字符串
	
	if( LCD.ShowNum_Mode == Fill_Zero)	// 多余位填充0模式
	{
		sprintf( Number_Buffer , "%0*.*lf",len,decs, decimals );	// 将 number 转换成字符串，便于显示		
	}
	else		// 多余位填充空格
	{
		sprintf( Number_Buffer , "%*.*lf",len,decs, decimals );	// 将 number 转换成字符串，便于显示		
	}
	
	LCD_DisplayString( x, y,(char *)Number_Buffer) ;	// 将转换得到的字符串显示出来
}


/***************************************************************************************************************************************
*	函 数 名: LCD_DrawLine
*
*	入口参数: x1 - 起点 水平坐标
*			 	 y1 - 起点 垂直坐标
*
*				 x2 - 终点 水平坐标
*            y2 - 终点 垂直坐标
*
*	函数功能: 在两点之间画线
*
*	说    明: 该函数移植于ST官方评估板的例程
*						 
*****************************************************************************************************************************************/

#define ABS(X)  ((X) > 0 ? (X) : -(X))    

void LCD_DrawLine(uint16_t x1, uint16_t y1, uint16_t x2, uint16_t y2)
{
	int16_t deltax = 0, deltay = 0, x = 0, y = 0, xinc1 = 0, xinc2 = 0, 
	yinc1 = 0, yinc2 = 0, den = 0, num = 0, numadd = 0, numpixels = 0, 
	curpixel = 0;

	deltax = ABS(x2 - x1);        /* The difference between the x's */
	deltay = ABS(y2 - y1);        /* The difference between the y's */
	x = x1;                       /* Start x off at the first pixel */
	y = y1;                       /* Start y off at the first pixel */

	if (x2 >= x1)                 /* The x-values are increasing */
	{
	 xinc1 = 1;
	 xinc2 = 1;
	}
	else                          /* The x-values are decreasing */
	{
	 xinc1 = -1;
	 xinc2 = -1;
	}

	if (y2 >= y1)                 /* The y-values are increasing */
	{
	 yinc1 = 1;
	 yinc2 = 1;
	}
	else                          /* The y-values are decreasing */
	{
	 yinc1 = -1;
	 yinc2 = -1;
	}

	if (deltax >= deltay)         /* There is at least one x-value for every y-value */
	{
	 xinc1 = 0;                  /* Don't change the x when numerator >= denominator */
	 yinc2 = 0;                  /* Don't change the y for every iteration */
	 den = deltax;
	 num = deltax / 2;
	 numadd = deltay;
	 numpixels = deltax;         /* There are more x-values than y-values */
	}
	else                          /* There is at least one y-value for every x-value */
	{
	 xinc2 = 0;                  /* Don't change the x for every iteration */
	 yinc1 = 0;                  /* Don't change the y when numerator >= denominator */
	 den = deltay;
	 num = deltay / 2;
	 numadd = deltax;
	 numpixels = deltay;         /* There are more y-values than x-values */
	}
	for (curpixel = 0; curpixel <= numpixels; curpixel++)
	{
	 LCD_DrawPoint(x,y,LCD.Color);             /* Draw the current pixel */
	 num += numadd;              /* Increase the numerator by the top of the fraction */
	 if (num >= den)             /* Check if numerator >= denominator */
	 {
		num -= den;               /* Calculate the new numerator value */
		x += xinc1;               /* Change the x as appropriate */
		y += yinc1;               /* Change the y as appropriate */
	 }
	 x += xinc2;                 /* Change the x as appropriate */
	 y += yinc2;                 /* Change the y as appropriate */
	}  
}

/***************************************************************************************************************************************
*	函 数 名: LCD_DrawLine_V
*
*	入口参数: x - 水平坐标
*			 	 y - 垂直坐标
*				 height - 垂直宽度
*
*	函数功能: 在指点位置绘制指定长宽的 垂直 线
*
*	说    明: 1. 该函数移植于ST官方评估板的例程
*				 2. 要绘制的区域不能超过屏幕的显示区域		
*            3. 如果只是画垂直的线，优先使用此函数，速度比 LCD_DrawLine 快很多
*  性能测试：
*****************************************************************************************************************************************/

void LCD_DrawLine_V(uint16_t x, uint16_t y, uint16_t height)
{
   uint16_t i ; // 计数变量

	for (i = 0; i < height; i++)
	{
       LCD_Buff[i] =  LCD.Color;  // 写入缓冲区
   }   
   LCD_SetAddress( x, y, x, y+height-1);	     // 设置坐标	

   LCD_WriteBuff(LCD_Buff,height);          // 写入显存
}

/***************************************************************************************************************************************
*	函 数 名: LCD_DrawLine_H
*
*	入口参数: x - 水平坐标
*			 	 y - 垂直坐标
*				 width  - 水平宽度
*
*	函数功能: 在指点位置绘制指定长宽的 水平 线
*
*	说    明: 1. 该函数移植于ST官方评估板的例程
*				 2. 要绘制的区域不能超过屏幕的显示区域		
*            3. 如果只是画 水平 的线，优先使用此函数，速度比 LCD_DrawLine 快很多
*  性能测试：
**********************************************************************************************************************************fanke*******/

void LCD_DrawLine_H(uint16_t x, uint16_t y, uint16_t width)
{
   uint16_t i ; // 计数变量

	for (i = 0; i < width; i++)
	{
       LCD_Buff[i] =  LCD.Color;  // 写入缓冲区
   }   
   LCD_SetAddress( x, y, x+width-1, y);	     // 设置坐标	

   LCD_WriteBuff(LCD_Buff,width);          // 写入显存
}
/***************************************************************************************************************************************
*	函 数 名: LCD_DrawRect
*
*	入口参数: x - 水平坐标
*			 	 y - 垂直坐标
*			 	 width  - 水平宽度
*				 height - 垂直宽度
*
*	函数功能: 在指点位置绘制指定长宽的矩形线条
*
*	说    明: 1. 该函数移植于ST官方评估板的例程
*				 2. 要绘制的区域不能超过屏幕的显示区域
*						 
*****************************************************************************************************************************************/

void LCD_DrawRect(uint16_t x, uint16_t y, uint16_t width, uint16_t height)
{
   // 绘制水平线
   LCD_DrawLine_H( x,  y,  width);           
   LCD_DrawLine_H( x,  y+height-1,  width);

   // 绘制垂直线
   LCD_DrawLine_V( x,  y,  height);
   LCD_DrawLine_V( x+width-1,  y,  height);
}


/***************************************************************************************************************************************
*	函 数 名: LCD_DrawCircle
*
*	入口参数: x - 圆心 水平坐标
*			 	 y - 圆心 垂直坐标
*			 	 r  - 半径
*
*	函数功能: 在坐标 (x,y) 绘制半径为 r 的圆形线条
*
*	说    明: 1. 该函数移植于ST官方评估板的例程
*				 2. 要绘制的区域不能超过屏幕的显示区域
*
*****************************************************************************************************************************************/

void LCD_DrawCircle(uint16_t x, uint16_t y, uint16_t r)
{
	int Xadd = -r, Yadd = 0, err = 2-2*r, e2;
	do {   

		LCD_DrawPoint(x-Xadd,y+Yadd,LCD.Color);
		LCD_DrawPoint(x+Xadd,y+Yadd,LCD.Color);
		LCD_DrawPoint(x+Xadd,y-Yadd,LCD.Color);
		LCD_DrawPoint(x-Xadd,y-Yadd,LCD.Color);
		
		e2 = err;
		if (e2 <= Yadd) {
			err += ++Yadd*2+1;
			if (-Xadd == Yadd && e2 <= Xadd) e2 = 0;
		}
		if (e2 > Xadd) err += ++Xadd*2+1;
    }
    while (Xadd <= 0);   
}


/***************************************************************************************************************************************
*	函 数 名: LCD_DrawEllipse
*
*	入口参数: x - 圆心 水平坐标
*			 	 y - 圆心 垂直坐标
*			 	 r1  - 水平半轴的长度
*				 r2  - 垂直半轴的长度
*
*	函数功能: 在坐标 (x,y) 绘制水平半轴为 r1 垂直半轴为 r2 的椭圆线条
*
*	说    明: 1. 该函数移植于ST官方评估板的例程
*				 2. 要绘制的区域不能超过屏幕的显示区域
*
*****************************************************************************************************************************************/

void LCD_DrawEllipse(int x, int y, int r1, int r2)
{
  int Xadd = -r1, Yadd = 0, err = 2-2*r1, e2;
  float K = 0, rad1 = 0, rad2 = 0;
   
  rad1 = r1;
  rad2 = r2;
  
  if (r1 > r2)
  { 
    do {
      K = (float)(rad1/rad2);
		 
		LCD_DrawPoint(x-Xadd,y+(uint16_t)(Yadd/K),LCD.Color);
		LCD_DrawPoint(x+Xadd,y+(uint16_t)(Yadd/K),LCD.Color);
		LCD_DrawPoint(x+Xadd,y-(uint16_t)(Yadd/K),LCD.Color);
		LCD_DrawPoint(x-Xadd,y-(uint16_t)(Yadd/K),LCD.Color);     
		 
      e2 = err;
      if (e2 <= Yadd) {
        err += ++Yadd*2+1;
        if (-Xadd == Yadd && e2 <= Xadd) e2 = 0;
      }
      if (e2 > Xadd) err += ++Xadd*2+1;
    }
    while (Xadd <= 0);
  }
  else
  {
    Yadd = -r2; 
    Xadd = 0;
    do { 
      K = (float)(rad2/rad1);

		LCD_DrawPoint(x-(uint16_t)(Xadd/K),y+Yadd,LCD.Color);
		LCD_DrawPoint(x+(uint16_t)(Xadd/K),y+Yadd,LCD.Color);
		LCD_DrawPoint(x+(uint16_t)(Xadd/K),y-Yadd,LCD.Color);
		LCD_DrawPoint(x-(uint16_t)(Xadd/K),y-Yadd,LCD.Color);  
		 
      e2 = err;
      if (e2 <= Xadd) {
        err += ++Xadd*3+1;
        if (-Yadd == Xadd && e2 <= Yadd) e2 = 0;
      }
      if (e2 > Yadd) err += ++Yadd*3+1;     
    }
    while (Yadd <= 0);
  }
}

/***************************************************************************************************************************************
*	函 数 名: LCD_FillCircle
*
*	入口参数: x - 圆心 水平坐标
*			 	 y - 圆心 垂直坐标
*			 	 r  - 半径
*
*	函数功能: 在坐标 (x,y) 填充半径为 r 的圆形区域
*
*	说    明: 1. 该函数移植于ST官方评估板的例程
*				 2. 要绘制的区域不能超过屏幕的显示区域
*
*****************************************************************************************************************************************/

void LCD_FillCircle(uint16_t x, uint16_t y, uint16_t r)
{
  int32_t  D;    /* Decision Variable */ 
  uint32_t  CurX;/* Current X Value */
  uint32_t  CurY;/* Current Y Value */ 
  
  D = 3 - (r << 1);
  
  CurX = 0;
  CurY = r;
  
  while (CurX <= CurY)
  {
    if(CurY > 0) 
    { 
      LCD_DrawLine_V(x - CurX, y - CurY,2*CurY);
      LCD_DrawLine_V(x + CurX, y - CurY,2*CurY);
    }
    
    if(CurX > 0) 
    {
		// LCD_DrawLine(x - CurY, y - CurX,x - CurY,y - CurX + 2*CurX);
		// LCD_DrawLine(x + CurY, y - CurX,x + CurY,y - CurX + 2*CurX); 	

      LCD_DrawLine_V(x - CurY, y - CurX,2*CurX);
      LCD_DrawLine_V(x + CurY, y - CurX,2*CurX);
    }
    if (D < 0)
    { 
      D += (CurX << 2) + 6;
    }
    else
    {
      D += ((CurX - CurY) << 2) + 10;
      CurY--;
    }
    CurX++;
  }
  LCD_DrawCircle(x, y, r);  
}

/***************************************************************************************************************************************
*	函 数 名: LCD_FillRect
*
*	入口参数: x - 水平坐标
*			 	 y - 垂直坐标
*			 	 width  - 水平宽度
*				 height -垂直宽度
*
*	函数功能: 在坐标 (x,y) 填充指定长宽的实心矩形
*
*	说    明: 要绘制的区域不能超过屏幕的显示区域
*						 
*****************************************************************************************************************************************/

void LCD_FillRect(uint16_t x, uint16_t y, uint16_t width, uint16_t height)
{
   LCD_SetAddress( x, y, x+width-1, y+height-1);	// 设置坐标	
	
	LCD_DC_Data;     // 数据指令选择 引脚输出高电平，代表本次传输 数据	

// 修改为16位数据宽度，写入数据更加效率，不需要拆分	
   LCD_SPI.Init.DataSize 	= SPI_DATASIZE_16BIT;   //	16位数据宽度
   HAL_SPI_Init(&LCD_SPI);		
	
   LCD_SPI_Transmit(&LCD_SPI, LCD.Color, width*height) ;

// 改回8位数据宽度，因为指令和部分数据都是按照8位传输的
	LCD_SPI.Init.DataSize 	= SPI_DATASIZE_8BIT;    //	8位数据宽度
   HAL_SPI_Init(&LCD_SPI);
}


/***************************************************************************************************************************************
*	函 数 名: LCD_DrawImage
*
*	入口参数: x - 起始水平坐标
*				 y - 起始垂直坐标
*			 	 width  - 图片的水平宽度
*				 height - 图片的垂直宽度
*				*pImage - 图片数据存储区的首地址
*
*	函数功能: 在指定坐标处显示图片
*
*	说    明: 1.要显示的图片需要事先进行取模、获悉图片的长度和宽度
*            2.使用 LCD_SetColor() 函数设置画笔色，LCD_SetBackColor() 设置背景色
*						 
*****************************************************************************************************************************************/

void 	LCD_DrawImage(uint16_t x,uint16_t y,uint16_t width,uint16_t height,const uint8_t *pImage) 
{  
   uint8_t   disChar;	         // 字模的值
	uint16_t  Xaddress = x;       // 水平坐标
 	uint16_t  Yaddress = y;       // 垂直坐标  
	uint16_t  i=0,j=0,m=0;        // 计数变量
	uint16_t  BuffCount = 0;      // 缓冲区计数
   uint16_t  Buff_Height = 0;    // 缓冲区的行数

// 因为缓冲区大小有限，需要分多次写入
   Buff_Height = (sizeof(LCD_Buff)/2) / height;    // 计算缓冲区能够写入图片的多少行

	for(i = 0; i <height; i++)             // 循环按行写入
	{
		for(j = 0; j <(float)width/8; j++)  
		{
			disChar = *pImage;

			for(m = 0; m < 8; m++)
			{ 
				if(disChar & 0x01)	
				{		
               LCD_Buff[BuffCount] =  LCD.Color;			// 当前模值不为0时，使用画笔色绘点
				}
				else		
				{		
				   LCD_Buff[BuffCount] = LCD.BackColor;		//否则使用背景色绘制点
				}
				disChar >>= 1;     // 模值移位
				Xaddress++;        // 水平坐标自加
				BuffCount++;       // 缓冲区计数       
				if( (Xaddress - x)==width ) // 如果水平坐标达到了字符宽度，则退出当前循环,进入下一行的绘制		
				{											 
					Xaddress = x;				                 
					break;
				}
			}	
			pImage++;			
		}
      if( BuffCount == Buff_Height*width  )  // 达到缓冲区所能容纳的最大行数时
      {
         BuffCount = 0; // 缓冲区计数清0

         LCD_SetAddress( x, Yaddress , x+width-1, Yaddress+Buff_Height-1);	// 设置坐标	
         LCD_WriteBuff(LCD_Buff,width*Buff_Height);          // 写入显存     

         Yaddress = Yaddress+Buff_Height;    // 计算行偏移，开始写入下一部分数据
      }     
      if( (i+1)== height ) // 到了最后一行时
      {
         LCD_SetAddress( x, Yaddress , x+width-1,i+y);	   // 设置坐标	
         LCD_WriteBuff(LCD_Buff,width*(i+1+y-Yaddress));    // 写入显存     
      }
	}	
}


/***************************************************************************************************************************************
*	函 数 名: LCD_CopyBuffer
*
*	入口参数: x - 起始水平坐标
*				 y - 起始垂直坐标
*			 	 width  - 目标区域的水平宽度
*				 height - 目标区域的垂直宽度
*				*pImage - 数据存储区的首地址
*
*	函数功能: 在指定坐标处，直接将数据复制到屏幕的显存
*
*	说    明: 批量复制函数，可用于移植 LVGL 或者将摄像头采集的图像显示出来
*						 
*****************************************************************************************************************************************/

void	LCD_CopyBuffer(uint16_t x, uint16_t y,uint16_t width,uint16_t height,uint16_t *DataBuff)
{
	
	LCD_SetAddress(x,y,x+width-1,y+height-1);

	LCD_DC_Data;     // 数据指令选择 引脚输出高电平，代表本次传输 数据	

// 修改为16位数据宽度，写入数据更加效率，不需要拆分	
   LCD_SPI.Init.DataSize 	= SPI_DATASIZE_16BIT;   //	16位数据宽度
   HAL_SPI_Init(&LCD_SPI);		
	
	LCD_SPI_TransmitBuffer(&LCD_SPI, DataBuff,width * height) ;
	
//	HAL_SPI_Transmit(&hspi5, (uint8_t *)DataBuff, (x2-x1+1) * (y2-y1+1), 1000) ;
	
// 改回8位数据宽度，因为指令和部分数据都是按照8位传输的
	LCD_SPI.Init.DataSize 	= SPI_DATASIZE_8BIT;    //	8位数据宽度
   HAL_SPI_Init(&LCD_SPI);		
	
}

/**********************************************************************************************************************************
*
* 以下几个函数修改于HAL的库函数，目的是为了SPI传输数据不限数据长度的写入，并且提高清屏的速度
*
*****************************************************************************************************************FANKE************/


/**
  * @brief Handle SPI Communication Timeout.
  * @param hspi: pointer to a SPI_HandleTypeDef structure that contains
  *              the configuration information for SPI module.
  * @param Flag: SPI flag to check
  * @param Status: flag state to check
  * @param Timeout: Timeout duration
  * @param Tickstart: Tick start value
  * @retval HAL status
  */
HAL_StatusTypeDef LCD_SPI_WaitOnFlagUntilTimeout(SPI_HandleTypeDef *hspi, uint32_t Flag, FlagStatus Status,
                                                    uint32_t Tickstart, uint32_t Timeout)
{
   /* Wait until flag is set */
   while ((__HAL_SPI_GET_FLAG(hspi, Flag) ? SET : RESET) == Status)
   {
      /* Check for the Timeout */
      if ((((HAL_GetTick() - Tickstart) >=  Timeout) && (Timeout != HAL_MAX_DELAY)) || (Timeout == 0U))
      {
         return HAL_TIMEOUT;
      }
   }
   return HAL_OK;
}


/**
 * @brief  Close Transfer and clear flags.
 * @param  hspi: pointer to a SPI_HandleTypeDef structure that contains
 *               the configuration information for SPI module.
 * @retval HAL_ERROR: if any error detected
 *         HAL_OK: if nothing detected
 */
 void LCD_SPI_CloseTransfer(SPI_HandleTypeDef *hspi)
{
  uint32_t itflag = hspi->Instance->SR;

  __HAL_SPI_CLEAR_EOTFLAG(hspi);
  __HAL_SPI_CLEAR_TXTFFLAG(hspi);

  /* Disable SPI peripheral */
  __HAL_SPI_DISABLE(hspi);

  /* Disable ITs */
  __HAL_SPI_DISABLE_IT(hspi, (SPI_IT_EOT | SPI_IT_TXP | SPI_IT_RXP | SPI_IT_DXP | SPI_IT_UDR | SPI_IT_OVR | SPI_IT_FRE | SPI_IT_MODF));

  /* Disable Tx DMA Request */
  CLEAR_BIT(hspi->Instance->CFG1, SPI_CFG1_TXDMAEN | SPI_CFG1_RXDMAEN);

  /* Report UnderRun error for non RX Only communication */
  if (hspi->State != HAL_SPI_STATE_BUSY_RX)
  {
    if ((itflag & SPI_FLAG_UDR) != 0UL)
    {
      SET_BIT(hspi->ErrorCode, HAL_SPI_ERROR_UDR);
      __HAL_SPI_CLEAR_UDRFLAG(hspi);
    }
  }

  /* Report OverRun error for non TX Only communication */
  if (hspi->State != HAL_SPI_STATE_BUSY_TX)
  {
    if ((itflag & SPI_FLAG_OVR) != 0UL)
    {
      SET_BIT(hspi->ErrorCode, HAL_SPI_ERROR_OVR);
      __HAL_SPI_CLEAR_OVRFLAG(hspi);
    }
  }

  /* SPI Mode Fault error interrupt occurred -------------------------------*/
  if ((itflag & SPI_FLAG_MODF) != 0UL)
  {
    SET_BIT(hspi->ErrorCode, HAL_SPI_ERROR_MODF);
    __HAL_SPI_CLEAR_MODFFLAG(hspi);
  }

  /* SPI Frame error interrupt occurred ------------------------------------*/
  if ((itflag & SPI_FLAG_FRE) != 0UL)
  {
    SET_BIT(hspi->ErrorCode, HAL_SPI_ERROR_FRE);
    __HAL_SPI_CLEAR_FREFLAG(hspi);
  }

  hspi->TxXferCount = (uint16_t)0UL;
  hspi->RxXferCount = (uint16_t)0UL;
}


/**
  * @brief  专为屏幕清屏而修改，将需要清屏的颜色批量传输
  * @param  hspi   : spi的句柄
  * @param  pData  : 要写入的数据
  * @param  Size   : 数据大小
  * @retval HAL status
  */

HAL_StatusTypeDef LCD_SPI_Transmit(SPI_HandleTypeDef *hspi,uint16_t pData, uint32_t Size)
{
   uint32_t    tickstart;  
   uint32_t    Timeout = 1000;      // 超时判断
   uint32_t    LCD_pData_32bit;     // 按32位传输时的数据
   uint32_t    LCD_TxDataCount;     // 传输计数
   HAL_StatusTypeDef errorcode = HAL_OK;

	/* Check Direction parameter */
	assert_param(IS_SPI_DIRECTION_2LINES_OR_1LINE_2LINES_TXONLY(hspi->Init.Direction));

	/* Process Locked */
	__HAL_LOCK(hspi);

	/* Init tickstart for timeout management*/
	tickstart = HAL_GetTick();

	if (hspi->State != HAL_SPI_STATE_READY)
	{
		errorcode = HAL_BUSY;
		__HAL_UNLOCK(hspi);
		return errorcode;
	}

	if ( Size == 0UL)
	{
		errorcode = HAL_ERROR;
		__HAL_UNLOCK(hspi);
		return errorcode;
	}

	/* Set the transaction information */
	hspi->State       = HAL_SPI_STATE_BUSY_TX;
	hspi->ErrorCode   = HAL_SPI_ERROR_NONE;

	LCD_TxDataCount   = Size;                // 传输的数据长度
	LCD_pData_32bit   = (pData<<16)|pData ;  // 按32位传输时，合并2个像素点的颜色  

	/*Init field not used in handle to zero */
	hspi->pRxBuffPtr  = NULL;
	hspi->RxXferSize  = (uint16_t) 0UL;
	hspi->RxXferCount = (uint16_t) 0UL;
	hspi->TxISR       = NULL;
	hspi->RxISR       = NULL;

	/* Configure communication direction : 1Line */
	if (hspi->Init.Direction == SPI_DIRECTION_1LINE)
	{
		SPI_1LINE_TX(hspi);
	}

// 不使用硬件 TSIZE 控制，此处设置为0，即不限制传输的数据长度
	MODIFY_REG(hspi->Instance->CR2, SPI_CR2_TSIZE, 0);

	/* Enable SPI peripheral */
	__HAL_SPI_ENABLE(hspi);

	if (hspi->Init.Mode == SPI_MODE_MASTER)
	{
		 /* Master transfer start */
		 SET_BIT(hspi->Instance->CR1, SPI_CR1_CSTART);
	}

	/* Transmit data in 16 Bit mode */
	while (LCD_TxDataCount > 0UL)
	{
		/* Wait until TXP flag is set to send data */
		if (__HAL_SPI_GET_FLAG(hspi, SPI_FLAG_TXP))
		{
			if ((hspi->TxXferCount > 1UL) && (hspi->Init.FifoThreshold > SPI_FIFO_THRESHOLD_01DATA))
			{
				*((__IO uint32_t *)&hspi->Instance->TXDR) = (uint32_t )LCD_pData_32bit;
				LCD_TxDataCount -= (uint16_t)2UL;
			}
			else
			{
				*((__IO uint16_t *)&hspi->Instance->TXDR) =  (uint16_t )pData;
				LCD_TxDataCount--;
			}
		}
		else
		{
			/* Timeout management */
			if ((((HAL_GetTick() - tickstart) >=  Timeout) && (Timeout != HAL_MAX_DELAY)) || (Timeout == 0U))
			{
				/* Call standard close procedure with error check */
				LCD_SPI_CloseTransfer(hspi);

				/* Process Unlocked */
				__HAL_UNLOCK(hspi);

				SET_BIT(hspi->ErrorCode, HAL_SPI_ERROR_TIMEOUT);
				hspi->State = HAL_SPI_STATE_READY;
				return HAL_ERROR;
			}
		}
	}

	if (LCD_SPI_WaitOnFlagUntilTimeout(hspi, SPI_SR_TXC, RESET, tickstart, Timeout) != HAL_OK)
	{
		SET_BIT(hspi->ErrorCode, HAL_SPI_ERROR_FLAG);
	}

	SET_BIT((hspi)->Instance->CR1 , SPI_CR1_CSUSP); // 请求挂起SPI传输
	/* 等待SPI挂起 */
	if (LCD_SPI_WaitOnFlagUntilTimeout(hspi, SPI_FLAG_SUSP, RESET, tickstart, Timeout) != HAL_OK)
	{
		SET_BIT(hspi->ErrorCode, HAL_SPI_ERROR_FLAG);
	}
	LCD_SPI_CloseTransfer(hspi);   /* Call standard close procedure with error check */

	SET_BIT((hspi)->Instance->IFCR , SPI_IFCR_SUSPC);  // 清除挂起标志位


	/* Process Unlocked */
	__HAL_UNLOCK(hspi);

	hspi->State = HAL_SPI_STATE_READY;

	if (hspi->ErrorCode != HAL_SPI_ERROR_NONE)
	{
		return HAL_ERROR;
	}
	return errorcode;
}

/**
  * @brief  专为批量写入数据修改，使之不限长度的传输数据
  * @param  hspi   : spi的句柄
  * @param  pData  : 要写入的数据
  * @param  Size   : 数据大小
  * @retval HAL status
  */
HAL_StatusTypeDef LCD_SPI_TransmitBuffer (SPI_HandleTypeDef *hspi, uint16_t *pData, uint32_t Size)
{
   uint32_t    tickstart;  
   uint32_t    Timeout = 1000;      // 超时判断
   uint32_t    LCD_TxDataCount;     // 传输计数
   HAL_StatusTypeDef errorcode = HAL_OK;

	/* Check Direction parameter */
	assert_param(IS_SPI_DIRECTION_2LINES_OR_1LINE_2LINES_TXONLY(hspi->Init.Direction));

	/* Process Locked */
	__HAL_LOCK(hspi);

	/* Init tickstart for timeout management*/
	tickstart = HAL_GetTick();

	if (hspi->State != HAL_SPI_STATE_READY)
	{
		errorcode = HAL_BUSY;
		__HAL_UNLOCK(hspi);
		return errorcode;
	}

	if ( Size == 0UL)
	{
		errorcode = HAL_ERROR;
		__HAL_UNLOCK(hspi);
		return errorcode;
	}

	/* Set the transaction information */
	hspi->State       = HAL_SPI_STATE_BUSY_TX;
	hspi->ErrorCode   = HAL_SPI_ERROR_NONE;

	LCD_TxDataCount   = Size;                // 传输的数据长度

	/*Init field not used in handle to zero */
	hspi->pRxBuffPtr  = NULL;
	hspi->RxXferSize  = (uint16_t) 0UL;
	hspi->RxXferCount = (uint16_t) 0UL;
	hspi->TxISR       = NULL;
	hspi->RxISR       = NULL;

	/* Configure communication direction : 1Line */
	if (hspi->Init.Direction == SPI_DIRECTION_1LINE)
	{
		SPI_1LINE_TX(hspi);
	}

// 不使用硬件 TSIZE 控制，此处设置为0，即不限制传输的数据长度
	MODIFY_REG(hspi->Instance->CR2, SPI_CR2_TSIZE, 0);

	/* Enable SPI peripheral */
	__HAL_SPI_ENABLE(hspi);

	if (hspi->Init.Mode == SPI_MODE_MASTER)
	{
		 /* Master transfer start */
		 SET_BIT(hspi->Instance->CR1, SPI_CR1_CSTART);
	}

	/* Transmit data in 16 Bit mode */
	while (LCD_TxDataCount > 0UL)
	{
		/* Wait until TXP flag is set to send data */
		if (__HAL_SPI_GET_FLAG(hspi, SPI_FLAG_TXP))
		{
			if ((LCD_TxDataCount > 1UL) && (hspi->Init.FifoThreshold > SPI_FIFO_THRESHOLD_01DATA))
			{
				*((__IO uint32_t *)&hspi->Instance->TXDR) = *((uint32_t *)pData);
				pData += 2;
				LCD_TxDataCount -= 2;
			}
			else
			{
				*((__IO uint16_t *)&hspi->Instance->TXDR) = *((uint16_t *)pData);
				pData += 1;
				LCD_TxDataCount--;
			}
		}
		else
		{
			/* Timeout management */
			if ((((HAL_GetTick() - tickstart) >=  Timeout) && (Timeout != HAL_MAX_DELAY)) || (Timeout == 0U))
			{
				/* Call standard close procedure with error check */
				LCD_SPI_CloseTransfer(hspi);

				/* Process Unlocked */
				__HAL_UNLOCK(hspi);

				SET_BIT(hspi->ErrorCode, HAL_SPI_ERROR_TIMEOUT);
				hspi->State = HAL_SPI_STATE_READY;
				return HAL_ERROR;
			}
		}
	}

	if (LCD_SPI_WaitOnFlagUntilTimeout(hspi, SPI_SR_TXC, RESET, tickstart, Timeout) != HAL_OK)
	{
		SET_BIT(hspi->ErrorCode, HAL_SPI_ERROR_FLAG);
	}

	SET_BIT((hspi)->Instance->CR1 , SPI_CR1_CSUSP); // 请求挂起SPI传输
	/* 等待SPI挂起 */
	if (LCD_SPI_WaitOnFlagUntilTimeout(hspi, SPI_FLAG_SUSP, RESET, tickstart, Timeout) != HAL_OK)
	{
		SET_BIT(hspi->ErrorCode, HAL_SPI_ERROR_FLAG);
	}
	LCD_SPI_CloseTransfer(hspi);   /* Call standard close procedure with error check */

	SET_BIT((hspi)->Instance->IFCR , SPI_IFCR_SUSPC);  // 清除挂起标志位


	/* Process Unlocked */
	__HAL_UNLOCK(hspi);

	hspi->State = HAL_SPI_STATE_READY;

	if (hspi->ErrorCode != HAL_SPI_ERROR_NONE)
	{
		return HAL_ERROR;
	}
	return errorcode;
}

/**************************************************************************************************************************************************************************************************************************************************************************FANKE***/
// 实验平台：反客 STM32H750核心板
//
