TheSuperPixel/Embedded_Core_Boards/STM32H750/测试例程/DCMI-摄像头OV5640驱动/图像显示到800x480分辨率的屏幕/Drivers/User/Inc/dcmi_ov5640_cfg.h

#ifndef __DCMI_OV2640_CFG_H
#define __DCMI_OV2640_CFG_H

#include "stm32h7xx_hal.h"

// 亮度等级，总共有9个等级，数字越大亮度越高
const uint8_t OV5640_Brightness_Config[][2]=
{
    {0x40, 0x09}, /* -4 */	
    {0x30, 0x09}, /* -3 */
    {0x20, 0x09}, /* -2 */
    {0x10, 0x09}, /* -1 */
    {0x00, 0x01}, /* +0 */
    {0x10, 0x01}, /* +1 */
    {0x20, 0x01}, /* +2 */
    {0x30, 0x01}, /* +3 */	
    {0x40, 0x01}, /* +4 */		 
};	

// 对比度等级，总共有7个等级，数字越大对比度越高
const uint8_t OV5640_Contrast_Config[][2]=
{
    {0x14, 0x14}, /* -3 */
    {0x18, 0x18}, /* -2 */
    {0x1c, 0x1c}, /* -1 */
    {0x20, 0x00}, /* +0 */
    {0x24, 0x10}, /* +1 */
    {0x28, 0x18}, /* +2 */
    {0x2c, 0x1c}, /* +3 */	
};	

// 特效设置,这里仅列举了4个模式，更多特效模式可以参考手册进行配置
const uint8_t OV5640_Effect_Config[][4]=
{
    {0x06, 0x40, 0x10, 0x08}, /* +0 正常模式*/
    {0x40, 0x08, 0x40, 0x10}, /* +1 负片模式*/
    {0x1e, 0x80, 0x80, 0x08}, /* +2 黑白模式*/
    {0x06, 0x40, 0x10, 0x09}, /* +3 正负片叠加模式*/	
};	

 
// OV5640初始化配置
const uint16_t OV5640_INIT_Config[][2]=
{
	{0x3008, 0x42}, // 系统电源控制，Bit[6]设置为1进入掉电模式，Bit[5:0]手册里没有说明作用
	{0x3103, 0x03}, // 系统时钟选择，设置使用PLL生成后的时钟，根据手册的配置，设置为0x03
	{0x3017, 0xff}, // PCLK、VS、HS以及数据引脚 D9~D6 使能输出
	{0x4740, 0X21}, // 设置PCLK、VS和HS的信号极性	
	{0x3018, 0xff}, // 数据引脚 D5~D0 使能输出

/*------- 时钟配置，可结合资料里的《时钟图》进行参考 -------------------------------------*/

//	以下所有关于时钟的配置，都是在 XVCLK=24MHz 的前提下进行设置
	
//	PLL预分频,bit[7:5]没有说明作用
//	bit[4], PLL R divider，用来设置是否将经过0x3035寄存器配置之后的时钟进行分频，设置为0不分频，为1则是2分频
// Bit[3:0]，PLL pre-divider，预分频，此处设置为3，即将 XVCLK 3分频后得到8M的时钟
	{0x3037, 0x13}, // 分频

// Bit[7:0] 用于设置倍频参数，倍频值可以是4~127的任何数值，大于127时，只能设置为偶数
// 此处设置为 100，即将上面分频得到的8M时钟进行100倍频得到800M时钟	
	{0x3036, 0x64}, // 倍频
	
// Bit[3:0] 用于设置MIPI时钟，这里用不到，保留默认值1
// Bit[7:4]	分频系数，此处设置为1，即不分频，此时主时钟还是800M，
// 如果需要降低帧率，可以设置为0x21，帧率会减半
	{0x3035, 0x11}, // 分频

// 接着回到 0x3037 的 bit[4] 设置，上面设置为1，即2分频，此时时钟为400M
// 0x3034的 Bit[3:0] 的取值会影响分频系数，设置为 8 是2分频，A是2.5分频，其它值则不分频
// 此处设置是2.5分频，此时主时钟为 160M
	{0x3034, 0x1A}, // 手册的默认值，0x1A
	
// 接下来这个寄存器是设置 PCLK（也就是DCMI接口里的像素时钟）	和 SCLK（应该是OV5640内部的各个处理单元的时钟）
// Bit[5:4]: PCLK 分频，此处为0，即不分频
// Bit[3:0] 都是和SCLK有关，直接使用手册给的参考值即可
	{0x3108, 0x01}, // 分频

// 0x460c寄存器的Bit[7:4]	用于设置JPEG空数据速度，默认值0x20	
// 0x460c寄存器的Bit[1]		用于设置PCLK的分频值，为0则是自动控制模式，设置为1时，PCLK的分频值由0x3824寄存器控制
// 自动模式下，生成的时钟非常高，通常都是80M，如果用户对EMC、 EMI有需求，可以手动调整
	{0x460c, 0x22},	
	
// Bit[4:0]有效，只能设置为 1、2、4、8、16 这几个分频值	
// 在上面的配置中，最终生成了160M的时钟，然后再根据0x3824寄存器的分频值得到最终的PCLK输出时钟
// STM32H750/743的DCMI接口所允许的最高速度为80M，所以不管是自动配置还是手动配置，都不能超过这个值
	{0x3824, 0x02}, 	// PCLK分频系数 ， 0x460c寄存器的Bit[1]	设置为1时才有效												fanke									
	
/*------------------------------------------------------------------  时钟配置结束 -----*/

// 手册里没有说明这些寄存器的作用,这里直接保留手册给的设置参数  
	{0x3630,0x36},	{0x3631,0x0e},	{0x3632,0xe2},	{0x3633,0x12},	{0x3621,0xe0},	{0x3704,0xa0},	// FanKe
	{0x3703,0x5a},	{0x3715,0x78},	{0x3717,0x01},	{0x370b,0x60},	{0x3705,0x1a},	{0x3905,0x02},
	{0x3906,0x10},	{0x3901,0x0a},	{0x3731,0x12},	{0x3600,0x08},	{0x3601,0x33},	{0x302d,0x60}, 
	{0x3620,0x52},	{0x371b,0x20},	{0x471c,0x50},	{0x3635,0x13},	{0x3636,0x03},	{0x3634,0x40},
	{0x3622,0x01},	{0x440e,0x00},	{0x5025,0x00}, {0x3618,0x00},	{0x3612,0x29},	{0x3708,0x64},	
	{0x3709,0x52},	{0x370c,0x03},	{0x302e,0x00}, {0x460b,0x37},	

	{0x3000, 0x00}, 	// 使能所有系统单元，包括 BIST、MCU、OTP等
	{0x3002, 0x1c}, 	// 复位 JFIFO, SFIFO, JPG	  
	{0x3004, 0xff}, 	// 使能所有系统单元，包括 BIST、MCU、OTP等
	{0x3006, 0xc3}, 	// 禁止 JPEG2x, JPEG	的时钟	 
	{0x300e, 0x58}, 	// 禁止 MIPI，使用DVP接口（也就是STM32的DCMI接口）


// 设置数据接口输出的格式，Bit[7:4]用于设置 RGB或者YUV等 格式，Bit[3:0]设置输出的序列，例如是BGR还是RGB
// 此处设置为RGB565格式，序列为 G[2:0]B[4:0], R[4:0]G[5:3]
	{0x4300, 0x6F}, 
// 除了要设置接口的输出格式，ISP（image sensor processor）图像处理单元也要设置成对应的格式	
	{0X501F, 0x01},	// ISP格式设置在Bit[2:0] ，此处使用RGB格式
	{0x5000, 0xa7}, 	// ISP设置，使能 LENC补偿、黑色像素、白色像素以及颜色插值（CIP）	 
	{0x5001, 0xA3},  	// ISP设置，使能 SDE特效、图像缩放、Color Matrix 色彩矩阵	、AWB 自动白平衡	
	           
   {0x3820, 0x47}, 	// Bit[2:1]用于设置是否垂直翻转，其余位的作用手册里没有说明
   {0x3821, 0x01}, 	// Bit[2:1]用于设置是否水平镜像，Bit[0]用于使能水平像素合并

/*------- 窗口配置，参考OV5640数据手册 4.2 小节 image windowing ------------------------*/

// OV5640有好几个窗口的概念
// 摄像头的物理像素窗口：2624*1954 （包含黑电平矫正线和空像素，有效分辨率为2592*1944）
// ISP（image sensor processor）输入窗口：需要进行处理的像素窗口
// 预缩放窗口：ISP窗口的基础上，调整用于缩放输出的窗口
// 输出窗口： 根据预缩放窗口和要输出的分辨率，进行缩放，得到最终的图像

// 因为摄像头的默认像素比例是 2592/1944 = 4/3 （15帧），而我们实际使用的屏幕往往不是这个比例或者不需要这么高像素，
// 因此需要做一定的调整，最终再配合DCMI的窗口裁剪以匹配屏幕。
// （注：用户也可以直接使用OV5640裁剪 物理窗口 得到对应比例的 ISP窗口，然后缩放偏移按照默认设置即可，
// 例如可以直接将ISP窗口设置为 240/280等对应实际屏幕的比例，而无需DCMI去裁剪。不过为了例程的通用性，我们选择
// 使用固定比例+DCMI裁剪的方式	）

// 以下配置为 16:9(1920*1080) 30帧 的配置
	0x3800, 0x01, // HS	1920 1080  30帧
	0x3801, 0x50, // HS
	0x3802, 0x01, // VS
	0x3803, 0xb2, // VS  
	0x3804, 0x08, // HW (HE)	
	0x3805, 0xef, // HW (HE)	
	0x3806, 0x05, // VH (VE)	ISP输入1951*1087
	0x3807, 0xf1, // VH (VE)
	0x380c, 0x09, // HTS			2500
	0x380d, 0xc4, // HTS			 
	0x380e, 0x04, // VTS			1120
	0x380f, 0x60, // VTS

	
// 以下配置为 4:3(2592*1944) 15帧 的配置
//	0x3800, 0x00, // HS
//	0x3801, 0x00, // HS
//	0x3802, 0x00, // VS
//	0x3803, 0x00, // 
//	0x3804, 0x0a, // HW (HE)	2623
//	0x3805, 0x3f, // HW (HE)
//	0x3806, 0x07, // VH (VE)
//	0x3807, 0x9F, // VH (VE)	
//	0x380c, 0x0B, // HTS	2844 = 2592+252
//	0x380d, 0x1C, // HTS
//	0x380e, 0x07, // VTS	1968 = 1944+24
//	0x380f, 0xB0, // VTS

	
	
// 预缩放窗口的设置，用于设置 在ISP窗口的基础上，根据偏移量的多少，得到预缩放窗口，
// 这里直接使用OV5640的默认配置，水平偏移16，垂直偏移4，因为包含了一些空像素和无效行，不能取0
   {0x3810,0x00}, // 水平偏移高字节
   {0x3811,0x10}, // 水平偏移低字节
   {0x3812,0x00},	// 垂直偏移高字节
   {0x3813,0x04},	// 垂直偏移低字节
	
// 以下两个寄存器，手册的描述是 水平和垂直二次采样时，奇数和偶数的增量，
// 笔者猜测的理解是：因为OV5640的全画幅分辨率很大，当实际输出的图像尺寸小于最大分辨率时，
// 需要通过裁剪或者2次采样，这两个寄存器用于控制每多少个像素去合并成一个像素，但是能找到
//	的信息有限，因此只能根据手册的给出的参考代码去配置
	{0x3814,0x11}, // timing X inc
	{0x3815,0x11}, // timing Y inc	
	
/*------------------------------------------------------------------  窗口配置结束 -----*/
	
// BLC（Black Level Calibration ）黑电平校正
// OV5640的像素阵列包含几条光学屏蔽(黑色)线，这些线被用作黑电平校准的参考，
// 不清楚要如何去配置，这里直接使用 OV5640应用指南 里的设置
	{0x4001,0x02}, {0x4004,0x02}, {0x4005,0x1a}, 

// 曝光时间相关
// 不清楚要如何去配置，这里使用的是 OpenMV 的配置
   {0x3a02,0x05},	{0x3a03,0xc4},	{0x3a08,0x00},	{0x3a09,0x93},	{0x3a0a,0x00},
   {0x3a0b,0x7b},	{0x3a0d,0x08}, {0x3a0e,0x06},	{0x3a14,0x05},	{0x3a15,0xc4},

// AEC 增益相关
// 不清楚要如何去配置，这里直接使用 OV5640应用指南 里的设置
	{0x3a13,0x43},	{0x3a18,0x00},	{0x3a19,0xf8}, 
	
// 50/60Hz 灯光条纹过滤 
// 不清楚要如何去配置，这里直接使用 OV5640应用指南 里的设置
	{0x3c01,0x34}, {0x3c04,0x28}, {0x3c05,0x98}, {0x3c06,0x00}, {0x3c07,0x08}, 
	{0x3c08,0x00}, {0x3c09,0x1c}, {0x3c0a,0x9c}, {0x3c0b,0x40}, 
	
// AWB 自动白平衡	
// 不清楚要如何去配置，这里直接使用 OV5640应用指南 里的设置
	{0x5180,0xff},	{0x5181,0xf2}, {0x5182,0x00},	{0x5183,0x14},	{0x5184,0x25},	{0x5185, 0x24},
	{0x5186,0x09},	{0x5187,0x09},	{0x5188,0x09},	{0x5189,0x75},	{0x518a,0x54},	{0x518b, 0xe0},
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
    0xc3, 0x12, 0x0e, 0xe9, 0x40, 0x02, 0xd2, 0x37, 0x75, 0x1f, 0x05, 0x22, 0x30, 0x01, 0x03, 0x02,
    0x04, 0xc0, 0x30, 0x02, 0x03, 0x02, 0x04, 0xc0, 0x90, 0x51, 0xa5, 0xe0, 0x78, 0x93, 0xf6, 0xa3,
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
}; 





#endif //__DCMI_OV2640_CFG_H
