TheSuperPixel/Embedded_Core_Boards/XC7A35T/测试例程/0_led_twinkle/led_twinkle.srcs/sources_1/new/led_twinkle.v

`timescale 1ns / 1ps

module led_twinkle(

input sys_clk,
input sys_rst_n,
output led
);

reg [25:0] cnt;

assign led=(cnt<26'd2500_0000)?1'b1:1'b0;

always @(posedge sys_clk or negedge sys_rst_n) begin
    if(!sys_rst_n)
        cnt<=26'd0;
    else if(cnt<5000_0000)
        cnt<=cnt+1'b1;
    else
        cnt<=26'd0;
end

endmodule
