TheSuperPixel/Embedded_Core_Boards/XC7A35T/测试例程/10_flow_led/rtl/flow_led.v

//****************************************Copyright (c)***********************************//
//原子哥在线教学平台：www.yuanzige.com
//技术支持：http://www.openedv.com/forum.php
//淘宝店铺：https://zhengdianyuanzi.tmall.com
//关注微信公众平台微信号："正点原子"，免费获取ZYNQ & FPGA & STM32 & LINUX资料。
//版权所有，盗版必究。
//Copyright(C) 正点原子 2023-2033
//All rights reserved                                  
//----------------------------------------------------------------------------------------
// File name:           flow_led
// Created by:          正点原子
// Created date:        2023年2月22日14:17:02
// Version:             V1.0
// Descriptions:        流水灯实验
//
//----------------------------------------------------------------------------------------
//****************************************************************************************//

module  flow_led(
    //input
    input              sys_clk,    //系统时钟
    input              sys_rst_n,  //系统复位信号，低电平有效
    
    //output    
    output  reg [4:0]  led
    );

//reg define
reg  [24:0]  cnt;    

//*****************************************************
//**                    main code
//*****************************************************

//计数器计时0.5s
always @(posedge sys_clk or negedge sys_rst_n) begin
    if(!sys_rst_n) 
        cnt <= 25'd0;
    else if(cnt < (25'd25000000 - 25'd1))   
        cnt <= cnt + 25'd1;
    else
        cnt <= 25'd0;
end

//LED移位控制  
always @(posedge sys_clk or negedge sys_rst_n) begin
    if(!sys_rst_n)
        led <= 5'b0001;
    else if(cnt == (25'd25000000 - 25'd1))
        led <= {led[3:0],led[4]};
    else 
        led <= led;
end

endmodule
