TheSuperPixel/Embedded_Core_Boards/XC7A35T/测试例程/44_top_sd_rw/prj/top_sd_rw.srcs/sources_1/ip/clk_wiz_0/clk_wiz_0_stub.v

// Copyright 1986-2020 Xilinx, Inc. All Rights Reserved.
// --------------------------------------------------------------------------------
// Tool Version: Vivado v.2020.2 (win64) Build 3064766 Wed Nov 18 09:12:45 MST 2020
// Date        : Fri Aug 25 09:29:01 2023
// Host        : DESKTOP-HN5R6GK running 64-bit major release  (build 9200)
// Command     : write_verilog -force -mode synth_stub
//               f:/ywd/dmvivado/sd/35_top_sd_rw/top_sd_rw.srcs/sources_1/ip/clk_wiz_0/clk_wiz_0_stub.v
// Design      : clk_wiz_0
// Purpose     : Stub declaration of top-level module interface
// Device      : xc7a35tfgg484-2
// --------------------------------------------------------------------------------

// This empty module with port declaration file causes synthesis tools to infer a black box for IP.
// The synthesis directives are for Synopsys Synplify support to prevent IO buffer insertion.
// Please paste the declaration into a Verilog source file or add the file as an additional source.
module clk_wiz_0(clk_out1, clk_out2, clk_out3, reset, locked, 
  clk_in1)
/* synthesis syn_black_box black_box_pad_pin="clk_out1,clk_out2,clk_out3,reset,locked,clk_in1" */;
  output clk_out1;
  output clk_out2;
  output clk_out3;
  input reset;
  output locked;
  input clk_in1;
endmodule
