TheSuperPixel/Embedded_Core_Boards/XC7A35T/测试例程/44_top_sd_rw/prj/top_sd_rw.srcs/sources_1/ip/clk_wiz_0/clk_wiz_0_stub.vhdl

-- Copyright 1986-2020 Xilinx, Inc. All Rights Reserved.
-- --------------------------------------------------------------------------------
-- Tool Version: Vivado v.2020.2 (win64) Build 3064766 Wed Nov 18 09:12:45 MST 2020
-- Date        : Fri Aug 25 09:29:01 2023
-- Host        : DESKTOP-HN5R6GK running 64-bit major release  (build 9200)
-- Command     : write_vhdl -force -mode synth_stub
--               f:/ywd/dmvivado/sd/35_top_sd_rw/top_sd_rw.srcs/sources_1/ip/clk_wiz_0/clk_wiz_0_stub.vhdl
-- Design      : clk_wiz_0
-- Purpose     : Stub declaration of top-level module interface
-- Device      : xc7a35tfgg484-2
-- --------------------------------------------------------------------------------
library IEEE;
use IEEE.STD_LOGIC_1164.ALL;

entity clk_wiz_0 is
  Port ( 
    clk_out1 : out STD_LOGIC;
    clk_out2 : out STD_LOGIC;
    clk_out3 : out STD_LOGIC;
    reset : in STD_LOGIC;
    locked : out STD_LOGIC;
    clk_in1 : in STD_LOGIC
  );

end clk_wiz_0;

architecture stub of clk_wiz_0 is
attribute syn_black_box : boolean;
attribute black_box_pad_pin : string;
attribute syn_black_box of stub : architecture is true;
attribute black_box_pad_pin of stub : architecture is "clk_out1,clk_out2,clk_out3,reset,locked,clk_in1";
begin
end;
