TheSuperPixel/Embedded_Core_Boards/XC7A35T/测试例程/44_top_sd_rw/prj/top_sd_rw.srcs/sources_1/ip/ila_0/ila_0_stub.vhdl

-- Copyright 1986-2020 Xilinx, Inc. All Rights Reserved.
-- --------------------------------------------------------------------------------
-- Tool Version: Vivado v.2020.2 (win64) Build 3064766 Wed Nov 18 09:12:45 MST 2020
-- Date        : Fri Jul  7 15:11:28 2023
-- Host        : DESKTOP-HN5R6GK running 64-bit major release  (build 9200)
-- Command     : write_vhdl -force -mode synth_stub
--               f:/ywd/dmvivado/sd/35_top_sd_rw/top_sd_rw.srcs/sources_1/ip/ila_0/ila_0_stub.vhdl
-- Design      : ila_0
-- Purpose     : Stub declaration of top-level module interface
-- Device      : xc7a35tfgg484-2
-- --------------------------------------------------------------------------------
library IEEE;
use IEEE.STD_LOGIC_1164.ALL;

entity ila_0 is
  Port ( 
    clk : in STD_LOGIC;
    probe0 : in STD_LOGIC_VECTOR ( 0 to 0 );
    probe1 : in STD_LOGIC_VECTOR ( 1 downto 0 );
    probe2 : in STD_LOGIC_VECTOR ( 2 downto 0 );
    probe3 : in STD_LOGIC_VECTOR ( 3 downto 0 );
    probe4 : in STD_LOGIC_VECTOR ( 4 downto 0 )
  );

end ila_0;

architecture stub of ila_0 is
attribute syn_black_box : boolean;
attribute black_box_pad_pin : string;
attribute syn_black_box of stub : architecture is true;
attribute black_box_pad_pin of stub : architecture is "clk,probe0[0:0],probe1[1:0],probe2[2:0],probe3[3:0],probe4[4:0]";
attribute X_CORE_INFO : string;
attribute X_CORE_INFO of stub : architecture is "ila,Vivado 2020.2";
begin
end;
