TheSuperPixel/Embedded_Core_Boards/XC7A35T/测试例程/48_mdio_eth_gpio_test/led_twinkle.srcs/constrs_1/new/led.xdc

#时序约束
create_clock -period 20.000 -name sys_clk -waveform {0.000 10.000} [get_ports sys_clk]

#IO管脚约束
set_property -dict {PACKAGE_PIN R4 IOSTANDARD LVCMOS33} [get_ports sys_clk]
set_property -dict {PACKAGE_PIN U2 IOSTANDARD LVCMOS33} [get_ports sys_rst_n]

#核心板LED
set_property -dict {PACKAGE_PIN F15 IOSTANDARD LVCMOS33} [get_ports led]

set_property -dict {PACKAGE_PIN AB21 IOSTANDARD LVCMOS33} [get_ports {phy_gpio[0]}]
set_property -dict {PACKAGE_PIN W19 IOSTANDARD LVCMOS33} [get_ports {phy_gpio[1]}]
set_property -dict {PACKAGE_PIN T20 IOSTANDARD LVCMOS33} [get_ports {phy_gpio[2]}]
set_property -dict {PACKAGE_PIN AA20 IOSTANDARD LVCMOS33} [get_ports {phy_gpio[3]}]
set_property -dict {PACKAGE_PIN AA21 IOSTANDARD LVCMOS33} [get_ports {phy_gpio[4]}]
set_property -dict {PACKAGE_PIN R19 IOSTANDARD LVCMOS33} [get_ports {phy_gpio[5]}]
set_property -dict {PACKAGE_PIN P19 IOSTANDARD LVCMOS33} [get_ports {phy_gpio[6]}]

set_property -dict {PACKAGE_PIN V19 IOSTANDARD LVCMOS33} [get_ports {phy_gpio[7]}]
set_property -dict {PACKAGE_PIN T18 IOSTANDARD LVCMOS33} [get_ports {phy_gpio[8]}]
set_property -dict {PACKAGE_PIN V18 IOSTANDARD LVCMOS33} [get_ports {phy_gpio[9]}]
set_property -dict {PACKAGE_PIN U18 IOSTANDARD LVCMOS33} [get_ports {phy_gpio[10]}]
set_property -dict {PACKAGE_PIN U17 IOSTANDARD LVCMOS33} [get_ports {phy_gpio[11]}]
set_property -dict {PACKAGE_PIN Y22 IOSTANDARD LVCMOS33} [get_ports {phy_gpio[12]}]



set_property -dict {PACKAGE_PIN AB22 IOSTANDARD LVCMOS33} [get_ports {phy_gpio[13]}]
set_property -dict {PACKAGE_PIN Y21 IOSTANDARD LVCMOS33} [get_ports {phy_gpio[14]}]
#固化
set_property CFGBVS VCCO [current_design]
set_property CONFIG_VOLTAGE 3.3 [current_design]
set_property BITSTREAM.GENERAL.COMPRESS true [current_design]
set_property BITSTREAM.CONFIG.CONFIGRATE 50 [current_design]
set_property BITSTREAM.CONFIG.SPI_BUSWIDTH 4 [current_design]
set_property BITSTREAM.CONFIG.SPI_FALL_EDGE Yes [current_design]
